BoujeeEnjinia1701/drumpanel/cad/drawings/DMP-DWG-001.pdf

CONCEPT, NOT FOR FABRICATION | DrumPanel · github.com/BoujeeEnjinia1701/drumpanel

FRONT VIEW
Scale 1:50; looking at the front (along +Y)

TOP VIEW
Scale 1:50; looking down (along -Z)

RIGHT VIEW
Scale 1:50; looking at the right side (along -X)

2182

4665 1340

ISOMETRIC VIEW
Not to scale; drums and panels not shown; seen from the front right and above, about 30 deg elevation

KEY DIMENSIONS (MM) AND DATA
Layout 2182 x 4665 x 1340 high (three stations in a row)
Drain stand at y -1500; saddles 500 apart; 2.9 deg fall to the bung end Cradle: rollers 380 apart at 310 high, under the hoops at +/-147
Drum axis 603; drum top 890; contact 33 deg from vertical
Rail posts at +/-712.5; rail beam top 1300; tool shelf on left post Shear discs 101 x 10, overlap 1.0; crank 155, 2.33:1
Ring head bolted on for ring cuts, nips 233 or 234 apart
Notches by lever punch: ends 60 x 35, hoops 40 x 32
End cutter wheel 50; cut line 552 dia; crank 150
Slip roll at y +1950: rolls 60 dia x 900 face
Sheet line 900; bending roll 90 behind, set 13.4 up (trial) Bending screws M20 x 1.5, dial 0.025 mm a division, lock nut Pinch gears m3 x 20 T; chain #40, 13 to 39 T; crank 300 Panels 233 / 234 / 233 x 1800; heads 552 dia
Masses (est.): cradle 196 kg, slip roll 191 kg, stand 15 kg PRELIMINARY, NOT FOR FABRICATION
REV | DESCRIPTION | DATE | BY
P1 | Preliminary GA from the constructable TRL 3 model (DMP-DDR-002) | 2026-10-03 | AC
P2 | Notching punch, ring head, raised head drive, dial adjusters, tool shelf (DMP-DDR-003) | 2026-10-03 | AC
DRUMPANEL | github.com/BoujeeEnjinia1701/drumpanel

## Drum opening bench set: general arrangement of the three stations

DRAWING NO.
DMP-DWG-001

REV
P2

SHEET
1 of 1

SIZE

## ANSI B

SCALE
1:50

UNITS
mm
PROJECTION | DATE
2026-10-03

DRAWN
Amish Chadha

MATERIAL / NOTES
S275 RHS and plate; C45 rolls; D2 discs; bronze bushes. See bom/bom.csv
Licensed CERN-OHL-S-2.0 · Design Molecule Lab · designmolecule.com | Generated from cad/src; do not edit by hand
