BoujeeEnjinia1701/drumpanel/cad/drawings/DMP-DWG-105.pdf

### BUILD PLAN SKETCH, PLAN NOT YET BUILT DrumPanel · github.com/BoujeeEnjinia1701/drumpanel

FRONT VIEW
Scale 1:10; looking at the front (along +Y)

TOP VIEW
Scale 1:10; looking down (along -Z)

RIGHT VIEW
Scale 1:10; looking at the right side (along -X)

120

200 946

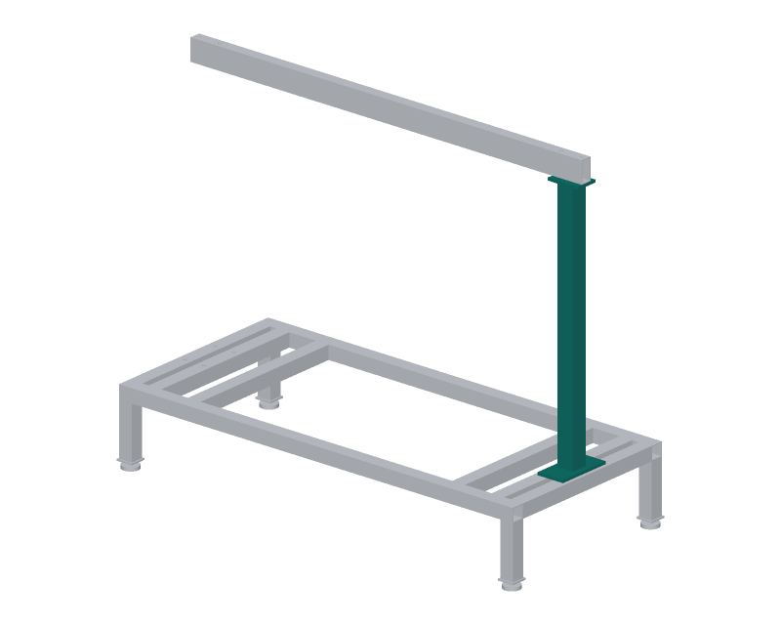
[picture p60: figure]

WHERE IT GOES
This part in colour, its neighbours in grey

HOW TO MAKE IT AND HOW IT FITS
Make two. Post: 60 x 60 x 4 mm RHS, 926.5 mm long, square ends. Base plate 200 x 100 x 10 mm: four 11 mm holes on a 75 x 140 mm rectangle (75 mm along the frame, 140 mm across it).
Cap plate 120 x 80 x 10 mm: two 11 mm holes on the centre line, 80 mm apart (40 mm each side of the post).
Weld the post to the middle of both plates, square both ways; check with a square before the welds cool.
Left post only: two 11 mm holes across it, 550 and 700 mm up from the frame top, for the tool shelf's two M10 through-bolts.
Fit: the base bolts across the two end cross members of the frame with 4 x M10 x 80; the rail beam sits on the cap and is held by
two M10 through-bolts. Post centre 712.5 mm from the middle. Check: post upright within 1 mm over its height when bolted.
REV | DESCRIPTION | DATE | BY
P1 | Making sketch for the prototype build plan | 2026-10-03 | AC
P2 | Amish's requirement decisions of 2026-10-03 (DMP-DDR-003) | 2026-10-03 | AC
DRUMPANEL | github.com/BoujeeEnjinia1701/drumpanel

## DrumPanel rail post (make 2): making sketch

DRAWING NO.
DMP-DWG-105

REV
P2

SHEET
1 of 1

SIZE

## ANSI B

SCALE
1:10

UNITS
mm
PROJECTION | DATE
2026-10-03

DRAWN
Amish Chadha

MATERIAL / NOTES
60 x 60 x 4 mm RHS; 10 mm plate; S275
Licensed CERN-OHL-S-2.0 · Design Molecule Lab · designmolecule.com | Generated from cad/src; do not edit by hand
