BoujeeEnjinia1701/drumpanel/cad/drawings/DMP-DWG-109.pdf

### BUILD PLAN SKETCH, PLAN NOT YET BUILT DrumPanel · github.com/BoujeeEnjinia1701/drumpanel

FRONT VIEW
Scale 1:5; looking at the front (along +Y)

TOP VIEW
Scale 1:5; looking down (along -Z)

RIGHT VIEW
Scale 1:5; looking at the right side (along -X)

195

148 272

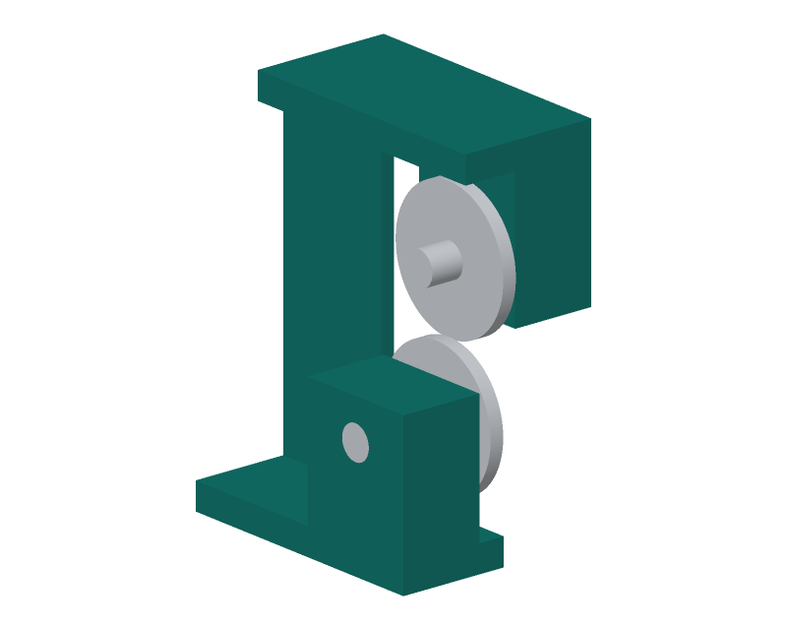
[picture p61: figure]

WHERE IT GOES
This part in colour, its neighbours in grey

HOW TO MAKE IT AND HOW IT FITS
Web: 10 mm plate 92 x 232 mm. It runs in the cut, behind the discs. Top plate 195 x 99 x 20 mm and lower plate 195 x 79 x 20 mm, welded across the top and bottom ends of the web.
Upper housing 90 x 60 x 101 mm on the top plate, beside the web; bore 57 mm on a line 49.5 mm above the nip for the eccentric bush (57 mm outside, 47 mm bore offset 3 mm) and one 6005 bearing. Lower housing 90 x 60 x 96 mm under the lower plate; bore 47 mm on a line 49.5 mm below the nip for two 6005 bearings.
Bore both housings in one setting so the shafts are parallel
within 0.05 mm over 60 mm; the disc faces must meet on one plane. Fit: the drop bar is welded to the top plate over the nip line;
four M8 tapped holes in the upper housing's outer face and the
top plate's end take the drive case. Make two frames: the second is the ring head (DMP-DWG-122).
Check: turning the eccentric moves the upper shaft 6 mm.
REV | DESCRIPTION | DATE | BY
P1 | Making sketch for the prototype build plan | 2026-10-03 | AC
P2 | Amish's requirement decisions of 2026-10-03 (DMP-DDR-003) | 2026-10-03 | AC
DRUMPANEL | github.com/BoujeeEnjinia1701/drumpanel

## DrumPanel rotary shear head frame: making sketch

DRAWING NO.
DMP-DWG-109

REV
P2

SHEET
1 of 1

SIZE

## ANSI B

SCALE
1:5

UNITS
mm
PROJECTION | DATE
2026-10-03

DRAWN
Amish Chadha

MATERIAL / NOTES
10 mm and 20 mm plate, S275; 6005-2RS bearings; eccentric bush
Licensed CERN-OHL-S-2.0 · Design Molecule Lab · designmolecule.com | Generated from cad/src; do not edit by hand
