BoujeeEnjinia1701/drumpanel/cad/drawings/DMP-DWG-110.pdf

### BUILD PLAN SKETCH, PLAN NOT YET BUILT DrumPanel · github.com/BoujeeEnjinia1701/drumpanel

FRONT VIEW
Scale 1:5; looking at the front (along +Y)

TOP VIEW
Scale 1:5; looking down (along -Z)

RIGHT VIEW
Scale 1:5; looking at the right side (along -X)

25

170 125

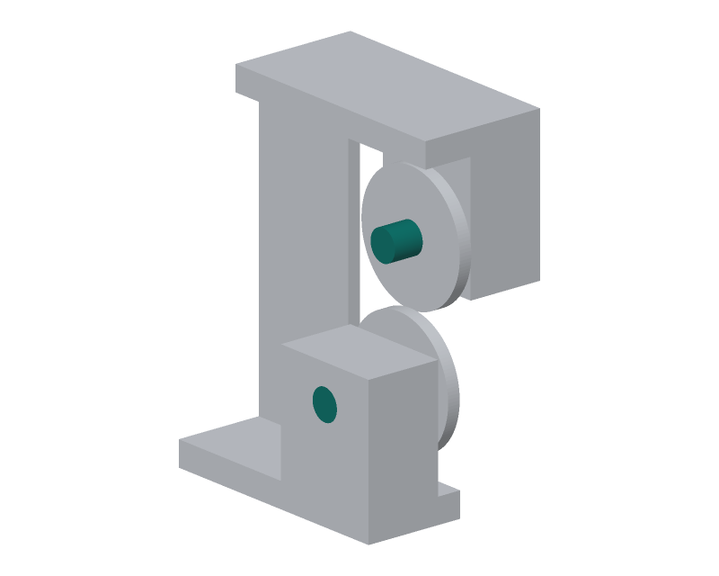
[picture p62: figure]

WHERE IT GOES
This part in colour, its neighbours in grey

HOW TO MAKE IT AND HOW IT FITS
Upper shaft: 25 mm, 120 mm long: a 24 mm stub on the disc side for the ring head coupling (a 6 mm cross slot in its end), a 35 mm shoulder at the disc, and a keyway at the far end for the 15 tooth sprocket inside the drive case.
Lower shaft: 25 mm, 74 mm long, with the same shoulder.
Discs (bought): 101 x 10 mm D2, hardened 58 to 60 HRC, 25 mm bore. Each is clamped against its shoulder by a countersunk M8 end screw and washer that sit below the cutting face (upper disc: a clamp collar on the stub instead).
Fit: cutting faces meet on the cut plane with no gap and no rub; shim behind a disc with 0.05 mm shims to get there.
Set the overlap to 1.0 mm with the eccentric and lock it.
Make a second set for the ring head (DMP-DWG-122).
REV | DESCRIPTION | DATE | BY
P1 | Making sketch for the prototype build plan | 2026-10-03 | AC
P2 | Amish's requirement decisions of 2026-10-03 (DMP-DDR-003) | 2026-10-03 | AC
DRUMPANEL | github.com/BoujeeEnjinia1701/drumpanel

## DrumPanel head shafts and discs: making sketch

DRAWING NO.
DMP-DWG-110

REV
P2

SHEET
1 of 1

SIZE

## ANSI B

SCALE
1:5

UNITS
mm
PROJECTION | DATE
2026-10-03

DRAWN
Amish Chadha

MATERIAL / NOTES
25 mm bright bar; bought D2 discs
Licensed CERN-OHL-S-2.0 · Design Molecule Lab · designmolecule.com | Generated from cad/src; do not edit by hand
