BoujeeEnjinia1701/drumpanel/cad/drawings/DMP-DWG-116.pdf

### BUILD PLAN SKETCH, PLAN NOT YET BUILT DrumPanel · github.com/BoujeeEnjinia1701/drumpanel

FRONT VIEW
Scale 1:10; looking at the front (along +Y)

TOP VIEW
Scale 1:10; looking down (along -Z)

RIGHT VIEW
Scale 1:10; looking at the right side (along -X)

1050

190 268

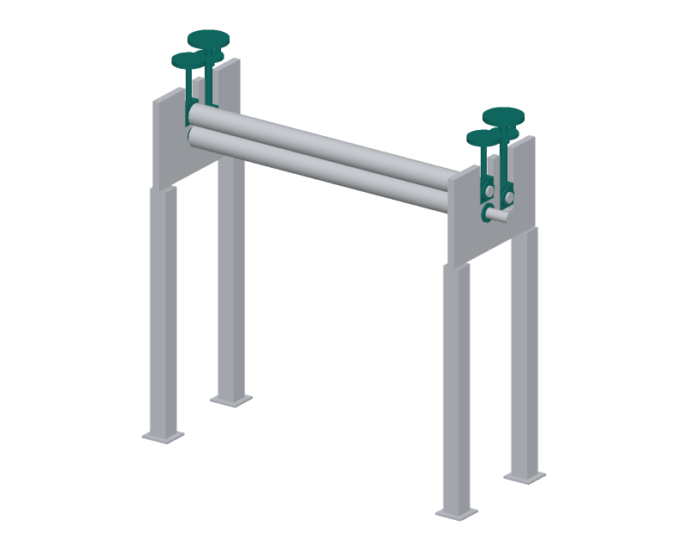
[picture p63: figure]

WHERE IT GOES
This part in colour, its neighbours in grey

HOW TO MAKE IT AND HOW IT FITS
Four slide blocks, 60 x 60 x 20 mm (20 mm thick = the side plate), bored 40 mm in the middle for a flanged bronze bush.
Fit in the 60 mm slots with 0.2 mm clearance; break the edges. Six flanged bronze bushes 30 x 40 x 20 mm, 52 mm flange 6 mm thick, pressed in from the outside; a grease hole in each.
A 3 mm keeper plate on the inside face holds each block in.
Pinch screws M16 x 120 (two) with 90 mm handwheels. Bending screws M20 x 1.5 fine pitch, 150 mm (two), with 110 mm handwheels. Each screw has a collar captured in the top of its block.
Bending roll adjuster on each bending screw: an M20 x 1.5 lock nut on the bridge; an 80 mm dial of 60 divisions (0.025 mm each), clamped to the screw by a set screw; a pointer screwed to the bridge, its tip over the dial rim.
Fit: the screws run in the threaded holes of the top bridges. Check: each block slides its full travel; one turn of a bending screw moves its roll 1.5 mm; the lock nut holds the setting.
REV | DESCRIPTION | DATE | BY
P1 | Making sketch for the prototype build plan | 2026-10-03 | AC
P2 | Amish's requirement decisions of 2026-10-03 (DMP-DDR-003) | 2026-10-03 | AC
DRUMPANEL | github.com/BoujeeEnjinia1701/drumpanel

## DrumPanel slide blocks, bushes, screws and dials: making sketch

DRAWING NO.
DMP-DWG-116

REV
P2

SHEET
1 of 1

SIZE

## ANSI B

SCALE
1:10

UNITS
mm
PROJECTION | DATE
2026-10-03

DRAWN
Amish Chadha

MATERIAL / NOTES
20 mm steel plate; bronze bushes; M16 and M20 x 1.5 screws; dials
Licensed CERN-OHL-S-2.0 · Design Molecule Lab · designmolecule.com | Generated from cad/src; do not edit by hand
