BoujeeEnjinia1701/drumpanel/cad/drawings/DMP-DWG-120.pdf

### BUILD PLAN SKETCH, PLAN NOT YET BUILT DrumPanel · github.com/BoujeeEnjinia1701/drumpanel

FRONT VIEW
Scale 1:5; looking at the front (along +Y)

TOP VIEW
Scale 1:5; looking down (along -Z)

RIGHT VIEW
Scale 1:5; looking at the right side (along -X)

140

156 309

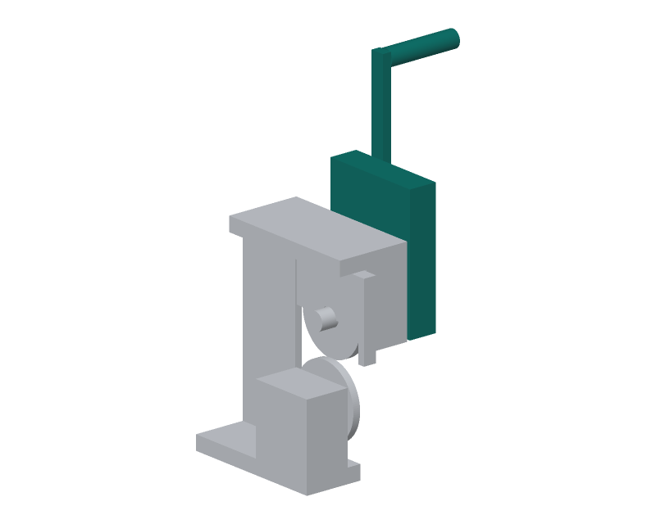
[picture p64: figure]

WHERE IT GOES
This part in colour, its neighbours in grey

HOW TO MAKE IT AND HOW IT FITS
Two plates 140 x 182 x 8 mm, 22 mm apart, joined by a 1.5 mm sheet band all round: the band is the chain guard.
Bores (both plates, drilled together): upper shaft 26 mm clear on the disc line; jackshaft 42 mm for a 6004 bearing, 80 mm above it; crank shaft 42 mm for a 6004 bearing, 60 mm back and 120 mm above the disc line.
Sprockets #35: 15 teeth on the upper shaft and on the jackshaft (first chain, 1 to 1); 28 teeth on the jackshaft and 12 teeth on
the crank shaft (second chain, 2.33 to 1).
Crank: 20 x 12 mm arm, 155 mm between centres, 24 mm grip 100 mm long free to spin; it turns well clear of the drum.
Fit: inner plate bolted to the upper housing and the top plate
with four M8 screws.
Check: 2.33 crank turns turn the discs once; nothing rubs.
REV | DESCRIPTION | DATE | BY
P1 | Making sketch for the prototype build plan | 2026-10-03 | AC
DRUMPANEL | github.com/BoujeeEnjinia1701/drumpanel

## DrumPanel shear head drive case and crank: making sketch

DRAWING NO.
DMP-DWG-120

REV
P1

SHEET
1 of 1

SIZE

## ANSI B

SCALE
1:5

UNITS
mm
PROJECTION | DATE
2026-10-03

DRAWN
Amish Chadha

MATERIAL / NOTES
8 mm plate; 1.5 mm sheet; 20 mm bar; #35 sprockets and chain; 6004-2RS bearings
Licensed CERN-OHL-S-2.0 · Design Molecule Lab · designmolecule.com | Generated from cad/src; do not edit by hand
