BoujeeEnjinia1701/drumpanel/cad/drawings/DMP-DWG-121.pdf

### BUILD PLAN SKETCH, PLAN NOT YET BUILT DrumPanel · github.com/BoujeeEnjinia1701/drumpanel

FRONT VIEW
Scale 1:5; looking at the front (along +Y)

TOP VIEW
Scale 1:5; looking down (along -Z)

RIGHT VIEW
Scale 1:5; looking at the right side (along -X)

435

76 200

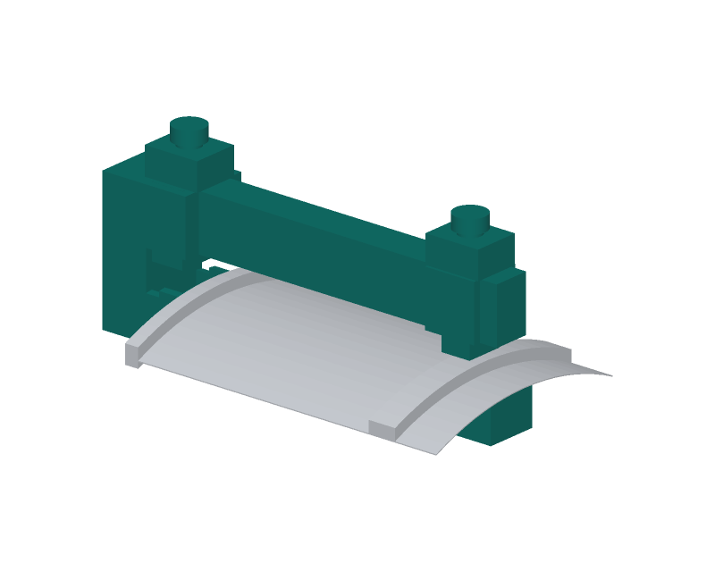
[picture p65: figure]

WHERE IT GOES
This part in colour, its neighbours in grey

HOW TO MAKE IT AND HOW IT FITS
C-frame from S355 plate: back 50 x 76 x 150 mm; lower jaw 56 x 50 mm and upper jaw 40 x 60 mm, 385 mm long; gap 40 mm. Die faces ground to the drum's inside radius (286 mm; 280 mm at the chime station).
Station 1, at the back: open-ended chime notch 60 x 35 mm. Station 2, 338 mm out: hoop slot 40 x 32 mm.
Punches D2, faces raked 10 degrees (roof shape); dies D2, punch to die clearance 0.1 to 0.2 mm a side; harden both.
Each punch is pushed by a Tr24 x 5 screw in a bronze nut block, through a needle thrust bearing; 500 mm ratchet lever.
Fit: chime: back face on the drum end. Hoop: drum end against the station 1 die block, jaw in through the chime notch.
Check: a punch enters its die by hand with even clearance.
REV | DESCRIPTION | DATE | BY
P1 | Making sketch for the prototype build plan | 2026-10-03 | AC
DRUMPANEL | github.com/BoujeeEnjinia1701/drumpanel

## DrumPanel lever notching punch: making sketch

DRAWING NO.
DMP-DWG-121

REV
P1

SHEET
1 of 1

SIZE

## ANSI B

SCALE
1:5

UNITS
mm
PROJECTION | DATE
2026-10-03

DRAWN
Amish Chadha

MATERIAL / NOTES
S355 plate; D2 punches and dies; Tr24 x 5 screws in bronze nuts
Licensed CERN-OHL-S-2.0 · Design Molecule Lab · designmolecule.com | Generated from cad/src; do not edit by hand
