BoujeeEnjinia1701/drumpanel/cad/drawings/DMP-DWG-122.pdf

### BUILD PLAN SKETCH, PLAN NOT YET BUILT DrumPanel · github.com/BoujeeEnjinia1701/drumpanel

FRONT VIEW
Scale 1:5; looking at the front (along +Y)

TOP VIEW
Scale 1:5; looking down (along -Z)

RIGHT VIEW
Scale 1:5; looking at the right side (along -X)

160

270 112

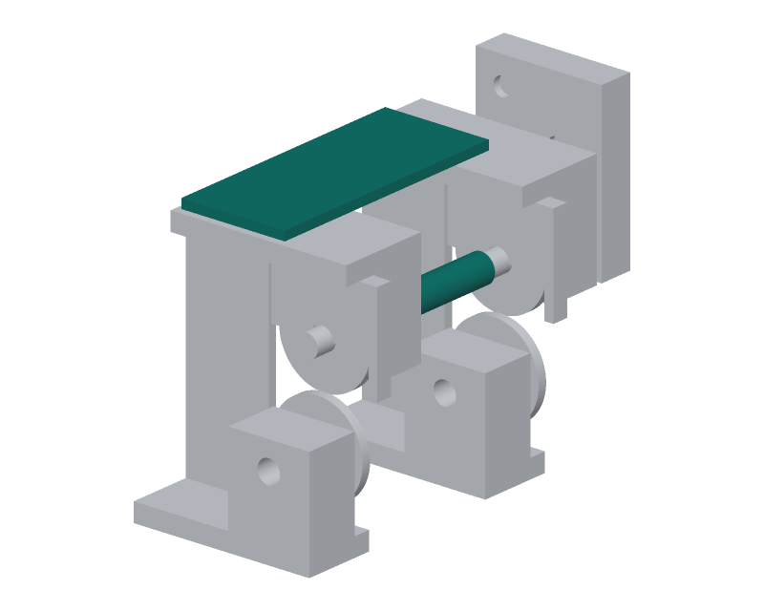
[picture p66: figure]

WHERE IT GOES
This part in colour, its neighbours in grey

HOW TO MAKE IT AND HOW IT FITS
The ring head is a second shear head made to DMP-DWG-109 to 111 with no drive; this sheet adds the parts that join it on.
Spacer plate 115 x 270 x 10 mm: four 13 mm holes over each top plate; the ring head end slotted so the nips sit 233 or 234 mm
apart (the middle pass is 234 mm).
Coupling shaft: 25 mm bar 135 mm long, a 6 mm dog across each end to engage the cross slots in the two upper shaft stubs.
Guard sleeve: loose plastic tube 31 mm outside over the coupling. Fit: with the main head swivelled for ring cuts, lower the ring
head through the slit, engage the coupling, bolt the plate.
Check: both upper discs turn together with the crank.
REV | DESCRIPTION | DATE | BY
P1 | Making sketch for the prototype build plan | 2026-10-03 | AC
DRUMPANEL | github.com/BoujeeEnjinia1701/drumpanel

## DrumPanel ring head spacer plate and coupling: making sketch

DRAWING NO.
DMP-DWG-122

REV
P1

SHEET
1 of 1

SIZE

## ANSI B

SCALE
1:5

UNITS
mm
PROJECTION | DATE
2026-10-03

DRAWN
Amish Chadha

MATERIAL / NOTES
10 mm plate; 25 mm bright bar; plastic tube
Licensed CERN-OHL-S-2.0 · Design Molecule Lab · designmolecule.com | Generated from cad/src; do not edit by hand
