BoujeeEnjinia1701/drumpanel/cad/drawings/DMP-DWG-123.pdf

### BUILD PLAN SKETCH, PLAN NOT YET BUILT DrumPanel · github.com/BoujeeEnjinia1701/drumpanel

FRONT VIEW
Scale 1:10; looking at the front (along +Y)

TOP VIEW
Scale 1:10; looking down (along -Z)

RIGHT VIEW
Scale 1:10; looking at the right side (along -X)

380

600 310

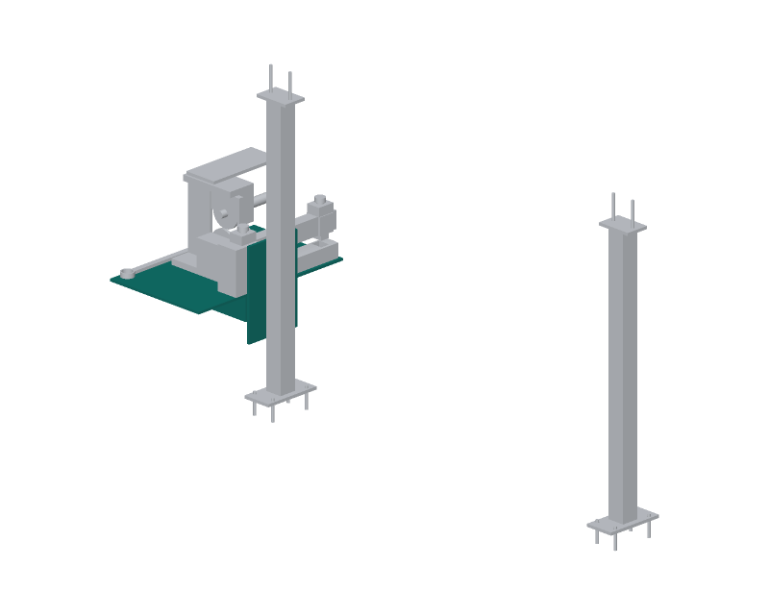
[picture p67: figure]

WHERE IT GOES
This part in colour, its neighbours in grey

HOW TO MAKE IT AND HOW IT FITS
Back plate 200 x 310 x 10 mm with two 11 mm holes on its centre line, 150 mm apart, matching the holes in the left post.
Shelf 380 x 600 x 6 mm, welded square to the back plate 150 mm above its bottom edge.
Two brackets 250 x 80 x 6 mm under the shelf, 200 mm apart, welded to the shelf and the back plate.
Fit: bolted to the outer face of the left post with two M10 through-bolts; the shelf top 608 mm from the floor.
It holds the notching punch, its lever and the ring head with its spacer plate and coupling (about 40 kg).
Check: level both ways; no movement when loaded by hand.
REV | DESCRIPTION | DATE | BY
P1 | Making sketch for the prototype build plan | 2026-10-03 | AC
DRUMPANEL | github.com/BoujeeEnjinia1701/drumpanel

## DrumPanel tool shelf on the left rail post: making sketch

DRAWING NO.
DMP-DWG-123

REV
P1

SHEET
1 of 1

SIZE

## ANSI B

SCALE
1:10

UNITS
mm
PROJECTION | DATE
2026-10-03

DRAWN
Amish Chadha

MATERIAL / NOTES
6 mm and 10 mm plate, S275; M10 bolts
Licensed CERN-OHL-S-2.0 · Design Molecule Lab · designmolecule.com | Generated from cad/src; do not edit by hand
