BoujeeEnjinia1701/drumpanel/cad/drawings/DMP-DWG-101.pdf

### BUILD PLAN SKETCH, PLAN NOT YET BUILT DrumPanel · github.com/BoujeeEnjinia1701/drumpanel

FRONT VIEW
Scale 1:10; looking at the front (along +Y)

TOP VIEW
Scale 1:10; looking down (along -Z)

RIGHT VIEW
Scale 1:10; looking at the right side (along -X)

800

560 410

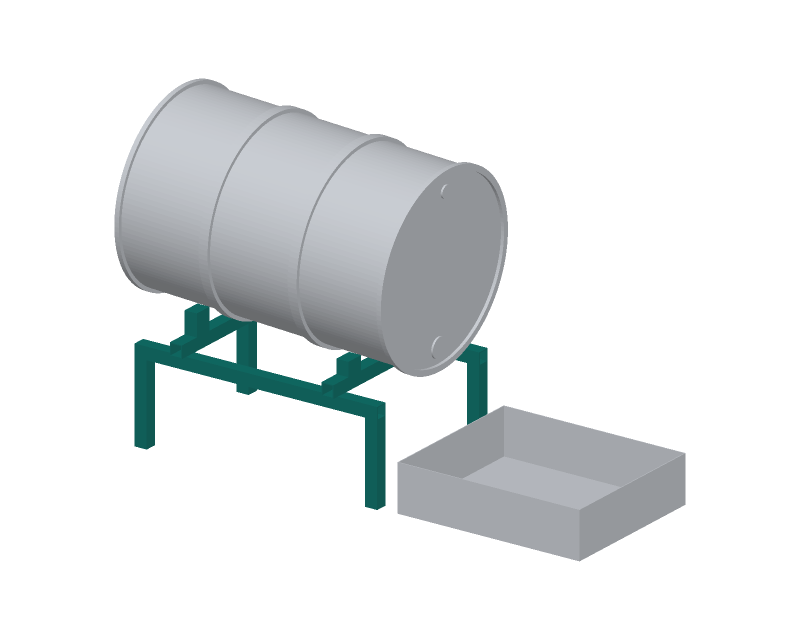
[picture p68: figure]

WHERE IT GOES
This part in colour, its neighbours in grey

HOW TO MAKE IT AND HOW IT FITS
Two rails 800 mm long, 480 mm apart (centres), on four legs 260 mm tall at the rail ends. Weld legs under the rails, square.
Two saddles 560 mm long across the rails, 500 mm apart (centres), welded on top of the rails. Top of the saddles 340 mm from the floor. Chocks: four hardwood blocks 40 x 60 mm, inner faces 300 mm apart. 70 mm tall on the far saddle, 45 mm tall on the bung-end saddle,
so the drum falls 2.9 degrees toward its bungs. Screw them down. Fit: the drum body rests on the four inner top edges of the chocks, bung end low and over the tray. Nothing else holds it.
Loads: a drum full of water is about 240 kg; 691 N on each chock. Check: frame stands level without rocking; the drum, rolled on, sits on all four chocks and does not roll off sideways.
REV | DESCRIPTION | DATE | BY
P1 | Making sketch for the prototype build plan | 2026-10-03 | AC
DRUMPANEL | github.com/BoujeeEnjinia1701/drumpanel

## DrumPanel drain and purge stand: making sketch

DRAWING NO.
DMP-DWG-101

REV
P1

SHEET
1 of 1

SIZE

## ANSI B

SCALE
1:10

UNITS
mm
PROJECTION | DATE
2026-10-03

DRAWN
Amish Chadha

MATERIAL / NOTES
40 x 40 x 3 mm RHS, S275; hardwood chocks 40 x 60 mm
Licensed CERN-OHL-S-2.0 · Design Molecule Lab · designmolecule.com | Generated from cad/src; do not edit by hand
