BoujeeEnjinia1701/drumpanel/cad/drawings/DMP-DWG-102.pdf

### BUILD PLAN SKETCH, PLAN NOT YET BUILT DrumPanel · github.com/BoujeeEnjinia1701/drumpanel

FRONT VIEW
Scale 1:20; looking at the front (along +Y)

TOP VIEW
Scale 1:20; looking down (along -Z)

RIGHT VIEW
Scale 1:20; looking at the right side (along -X)

1560

710 248

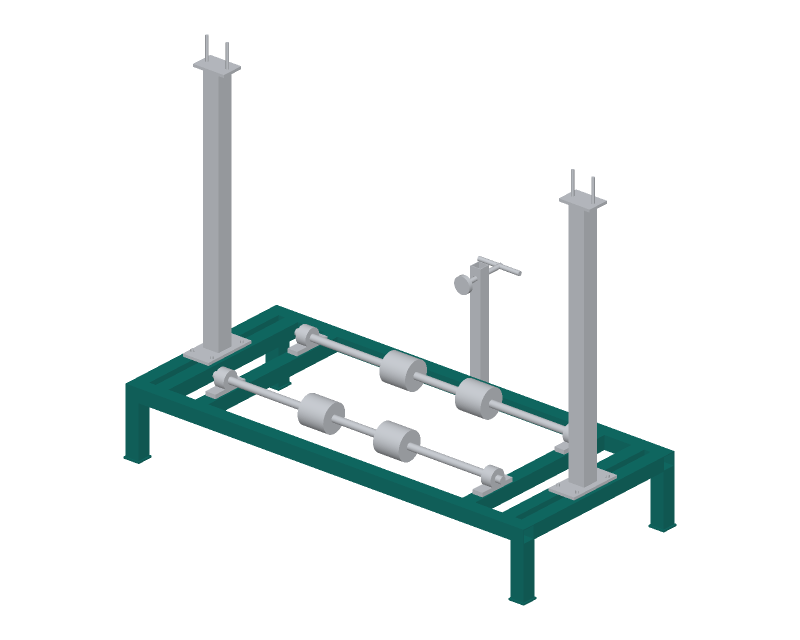
[picture p69: figure]

WHERE IT GOES
This part in colour, its neighbours in grey

HOW TO MAKE IT AND HOW IT FITS
Two side rails 1,550 mm long, outer faces 700 mm apart.
Six cross members 600 mm long between the rails, centred 520, 675 and 750 mm each side of the middle (the last one flush with the ends). Four legs 192 mm long under the corners, each with a 60 x 60 x 6 mm foot plate and an M12 nut welded on it for a levelling foot.
Top of the frame 273.5 mm from the floor with the feet screwed in
13 mm. Weld on a flat table; check the diagonals agree within 2 mm. Holes, 11 mm: two for each pillow block on the 520 mm members, 137.5 and 242.5 mm each side of the centre line; four for each post base, 70 mm each side of the centre line on the 675 and 750 members. Fit: pillow blocks and post bases bolt on top with M10; the brake
post bolts to the outer face of a side rail at the middle.
Check: frame top flat within 2 mm when the feet are set.
REV | DESCRIPTION | DATE | BY
P1 | Making sketch for the prototype build plan | 2026-10-03 | AC
DRUMPANEL | github.com/BoujeeEnjinia1701/drumpanel

## DrumPanel cradle frame: making sketch

DRAWING NO.
DMP-DWG-102

REV
P1

SHEET
1 of 1

SIZE

## ANSI B

SCALE
1:20

UNITS
mm
PROJECTION | DATE
2026-10-03

DRAWN
Amish Chadha

MATERIAL / NOTES
50 x 50 x 3 mm RHS, S275; 6 mm foot plates; M12 nuts
Licensed CERN-OHL-S-2.0 · Design Molecule Lab · designmolecule.com | Generated from cad/src; do not edit by hand
