BoujeeEnjinia1701/drumpanel/cad/drawings/DMP-DWG-103.pdf

### BUILD PLAN SKETCH, PLAN NOT YET BUILT DrumPanel · github.com/BoujeeEnjinia1701/drumpanel

FRONT VIEW
Scale 1:10; looking at the front (along +Y)

TOP VIEW
Scale 1:10; looking down (along -Z)

RIGHT VIEW
Scale 1:10; looking at the right side (along -X)

1120

102 102

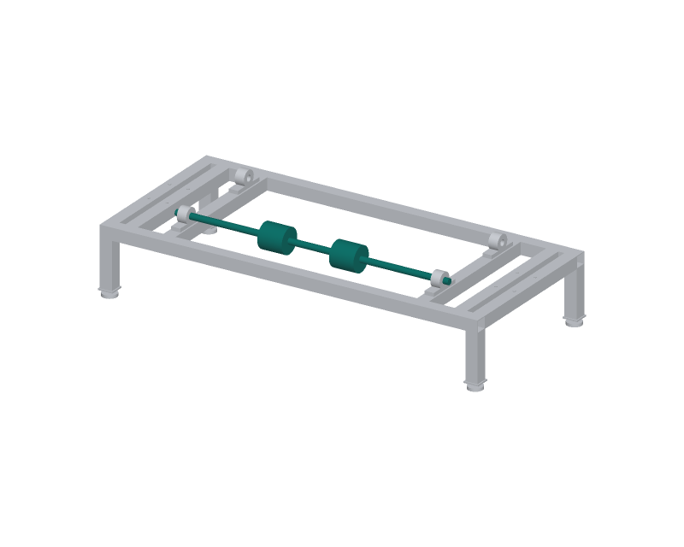
[picture p70: figure]

WHERE IT GOES
This part in colour, its neighbours in grey

HOW TO MAKE IT AND HOW IT FITS
Make two. Shaft: 25 mm bright bar, 1,120 mm long, ends chamfered. Rollers: 101.6 x 4 mm tube cut 100 mm long; two 10 mm discs
93 mm across, bored 25 mm, welded into each end of the tube. Slide two rollers on, centred 147 mm each side of the middle of the shaft (294 mm apart, under the drum's rolling hoops).
Weld each disc to the shaft all round; skim the roller faces true
in a lathe if they run out more than 0.5 mm.
Fit: the shaft runs in two UCP205 pillow blocks, 1,040 mm apart, grub screws tightened on the shaft. Shaft centres 380 mm apart. Check: the shaft turns freely by hand in its blocks; the rollers run true within 0.5 mm.
REV | DESCRIPTION | DATE | BY
P1 | Making sketch for the prototype build plan | 2026-10-03 | AC
DRUMPANEL | github.com/BoujeeEnjinia1701/drumpanel

## DrumPanel roller shaft with two rollers (make 2): making sketch

DRAWING NO.
DMP-DWG-103

REV
P1

SHEET
1 of 1

SIZE

## ANSI B

SCALE
1:10

UNITS
mm
PROJECTION | DATE
2026-10-03

DRAWN
Amish Chadha

MATERIAL / NOTES
25 mm bright steel bar; 101.6 x 4 mm tube; 10 mm plate discs
Licensed CERN-OHL-S-2.0 · Design Molecule Lab · designmolecule.com | Generated from cad/src; do not edit by hand
