BoujeeEnjinia1701/drumpanel/cad/drawings/DMP-DWG-104.pdf

### BUILD PLAN SKETCH, PLAN NOT YET BUILT DrumPanel · github.com/BoujeeEnjinia1701/drumpanel

FRONT VIEW
Scale 1:5; looking at the front (along +Y)

TOP VIEW
Scale 1:5; looking down (along -Z)

RIGHT VIEW
Scale 1:5; looking at the right side (along -X)

160

183 460

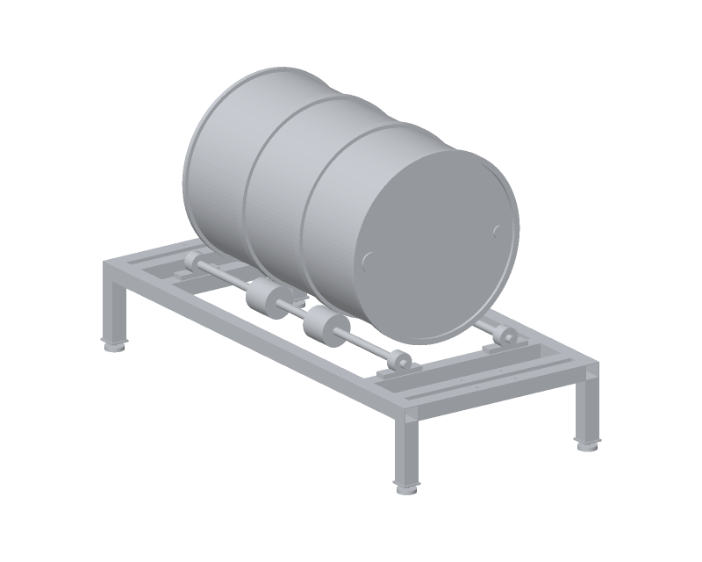
[picture p71: figure]

WHERE IT GOES
This part in colour, its neighbours in grey

HOW TO MAKE IT AND HOW IT FITS
Post: 40 x 40 x 3 mm RHS, 460 mm long. Two 11 mm holes through it, 25 mm apart, 56 and 81 mm up from its foot, to bolt it to the rail.
An 18 mm hole through both walls 423 mm up from its foot; weld an M16 nut over the hole on the outer face (away from the drum). Screw: M16 x 200; weld a 16 mm bar 160 mm long across its head as a T-handle. A 60 mm rubber pad 15 mm thick on a swivel plate at its tip faces the drum.
Fit: post bolted with 2 x M10 to the outer face of the right side
rail at the middle of the frame. Screwed in, the pad presses on the drum side between the hoops at the height of the drum axis. Check: with the screw tight the drum cannot be turned by hand.
REV | DESCRIPTION | DATE | BY
P1 | Making sketch for the prototype build plan | 2026-10-03 | AC
DRUMPANEL | github.com/BoujeeEnjinia1701/drumpanel

## DrumPanel drum brake: making sketch

DRAWING NO.
DMP-DWG-104

REV
P1

SHEET
1 of 1

SIZE

## ANSI B

SCALE
1:5

UNITS
mm
PROJECTION | DATE
2026-10-03

DRAWN
Amish Chadha

MATERIAL / NOTES
40 x 40 x 3 mm RHS; M16 x 200 screw; 16 mm bar; rubber pad
Licensed CERN-OHL-S-2.0 · Design Molecule Lab · designmolecule.com | Generated from cad/src; do not edit by hand
