BoujeeEnjinia1701/drumpanel/cad/drawings/DMP-DWG-106.pdf

### BUILD PLAN SKETCH, PLAN NOT YET BUILT DrumPanel · github.com/BoujeeEnjinia1701/drumpanel

FRONT VIEW
Scale 1:10; looking at the front (along +Y)

TOP VIEW
Scale 1:10; looking down (along -Z)

RIGHT VIEW
Scale 1:10; looking at the right side (along -X)

1540

40 80

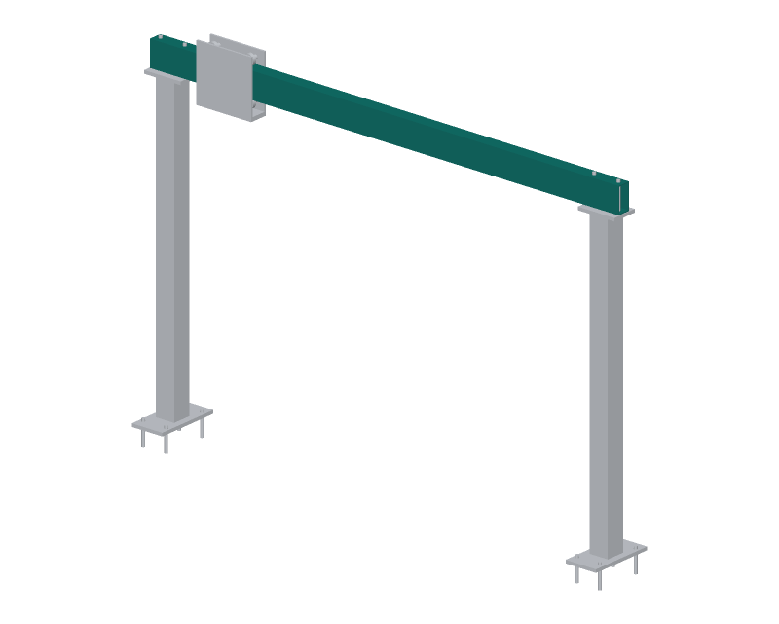
[picture p72: figure]

WHERE IT GOES
This part in colour, its neighbours in grey

HOW TO MAKE IT AND HOW IT FITS
Rail beam: 80 x 40 x 3 mm RHS, 1,540 mm long, stood on its narrow edge (80 mm tall). The top face is the trolley track: keep it
clean and free of weld spatter; file any seam bead flat.
Holes: two 11 mm vertical holes through both walls at each end, 17.5 and 97.5 mm from the end, on the centre line.
Crush tubes: 14 mm tube 74 mm long inside the beam at each hole so the through-bolts do not crush it.
Fit: each end sits on a post cap, held by two M10 x 110 bolts;
the bolt heads on top stop the trolley at the ends.
Check: the top face is straight within 1 mm over its length (a taut string or a straightedge).
REV | DESCRIPTION | DATE | BY
P1 | Making sketch for the prototype build plan | 2026-10-03 | AC
DRUMPANEL | github.com/BoujeeEnjinia1701/drumpanel

## DrumPanel rail beam: making sketch

DRAWING NO.
DMP-DWG-106

REV
P1

SHEET
1 of 1

SIZE

## ANSI B

SCALE
1:10

UNITS
mm
PROJECTION | DATE
2026-10-03

DRAWN
Amish Chadha

MATERIAL / NOTES
80 x 40 x 3 mm RHS, S275; 14 mm tube
Licensed CERN-OHL-S-2.0 · Design Molecule Lab · designmolecule.com | Generated from cad/src; do not edit by hand
