BoujeeEnjinia1701/drumpanel/cad/drawings/DMP-DWG-107.pdf

### BUILD PLAN SKETCH, PLAN NOT YET BUILT DrumPanel · github.com/BoujeeEnjinia1701/drumpanel

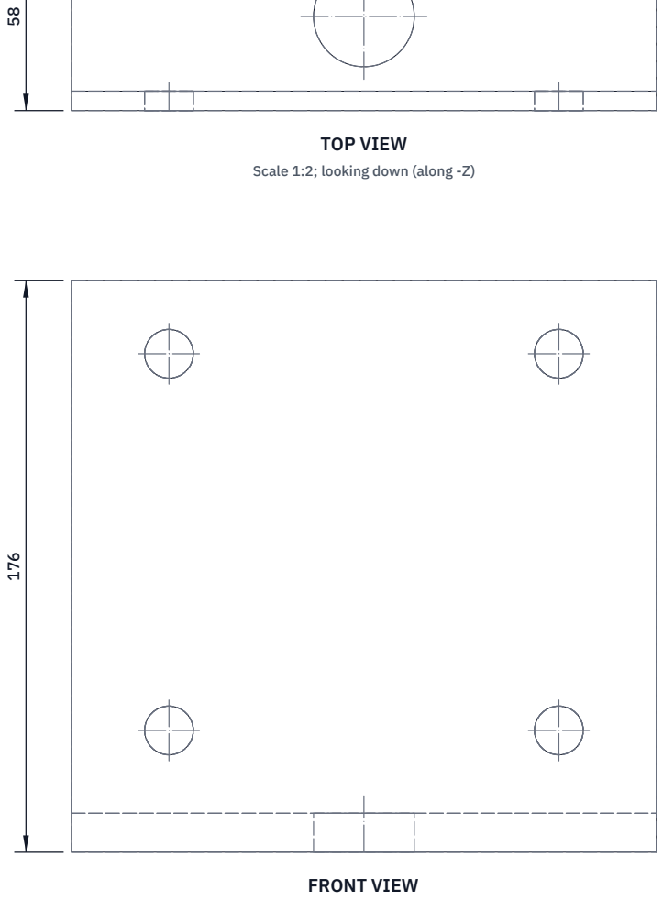
[picture p73: figure]
FRONT VIEW; TOP VIEW; Scale 1:2; looking down (along -Z)

Scale 1:2; looking at the front (along +Y)

RIGHT VIEW
Scale 1:2; looking at the right side (along -X)

180

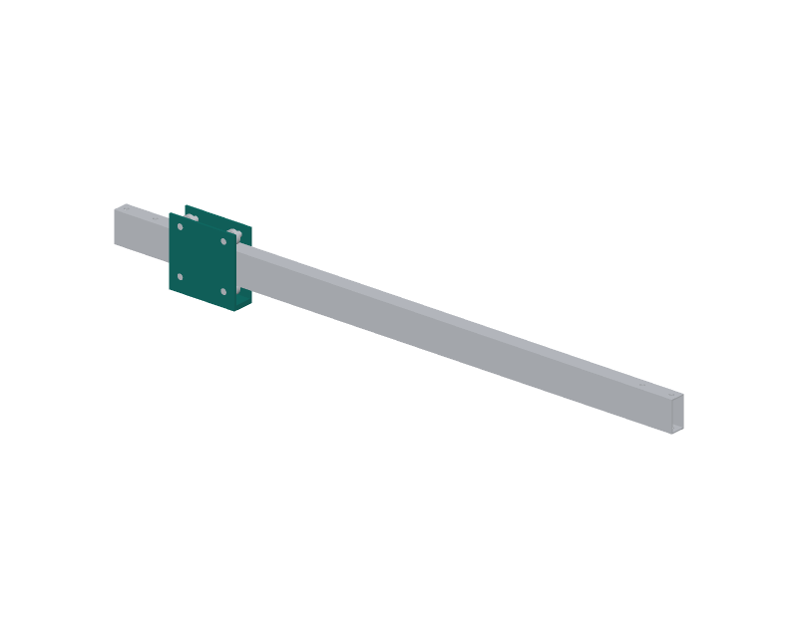
[picture p74: figure]

WHERE IT GOES
This part in colour, its neighbours in grey

HOW TO MAKE IT AND HOW IT FITS
Two side plates 180 x 164 x 6 mm. Four 15.5 mm axle holes in each, 60 mm each side of the middle, 141.5 and 25.5 mm up from the bottom edge. Drill the two plates clamped together.
Swivel plate 180 x 58 x 12 mm, welded under both side plates so their inner faces are 46 mm apart (beam 40 mm, 3 mm each side). Pivot hole 31 mm in the middle of the swivel plate; two 10.5 mm index holes 45 mm from it, at 0 and 90 degrees.
Wheels: 6202-2RS bearings on 15 mm axles with spacers; two ride on top of the beam and two run 1 mm under it (anti-lift).
Fit: slide on from the beam end before the end bolts go in, or
drop on from above and fit the lower axles after.
Check: rolls the full length by hand, no tight spots.
REV | DESCRIPTION | DATE | BY
P1 | Making sketch for the prototype build plan | 2026-10-03 | AC
DRUMPANEL | github.com/BoujeeEnjinia1701/drumpanel

## DrumPanel trolley with swivel plate: making sketch

DRAWING NO.
DMP-DWG-107

REV
P1

SHEET
1 of 1

SIZE

## ANSI B

SCALE
1:2

UNITS
mm
PROJECTION | DATE
2026-10-03

DRAWN
Amish Chadha

MATERIAL / NOTES
6 mm and 12 mm plate, S275; four 6202-2RS bearings; 15 mm bar
Licensed CERN-OHL-S-2.0 · Design Molecule Lab · designmolecule.com | Generated from cad/src; do not edit by hand
