BoujeeEnjinia1701/drumpanel/cad/drawings/DMP-DWG-108.pdf

### BUILD PLAN SKETCH, PLAN NOT YET BUILT DrumPanel · github.com/BoujeeEnjinia1701/drumpanel

FRONT VIEW
Scale 1:5; looking at the front (along +Y)

TOP VIEW
Scale 1:5; looking down (along -Z)

RIGHT VIEW
Scale 1:5; looking at the right side (along -X)

120

120 159

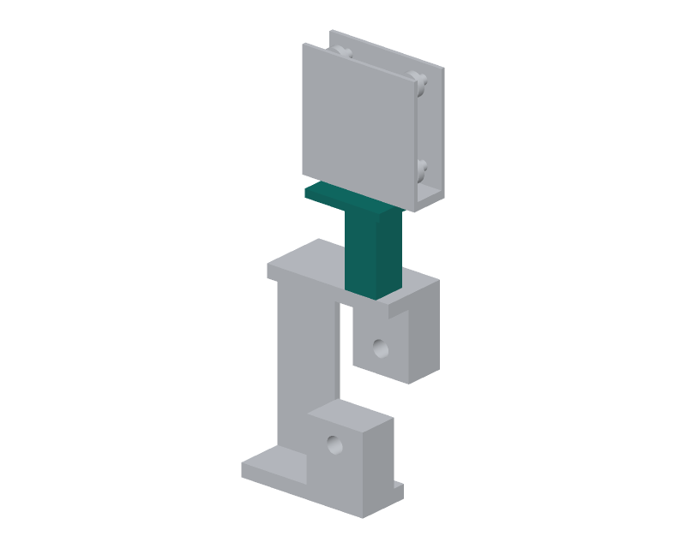
[picture p75: figure]

WHERE IT GOES
This part in colour, its neighbours in grey

HOW TO MAKE IT AND HOW IT FITS
Head plate 120 x 120 x 12 mm: a 31 mm hole in the middle for the pivot pin and a 10.5 mm hole 45 mm from it for the index pin. Drop bar: 50 x 50 x 4 mm RHS, 126 mm long, welded square under the head plate, centred, and at its lower end to the middle of
the shear head's top plate (over the nip line).
Pivot pin: 30 mm bar 55 mm long with a 40 mm collar welded at its top; a 6 mm hole for an R-clip under the swivel plate.
Index pin: 10 mm, on a lanyard, through the head plate into one of the two holes in the swivel plate: slit or ring position.
Fit: the head hangs from the trolley on the pivot pin and turns through 90 degrees when the index pin is out.
Check: the head swings freely; the index pin drops in at both positions.
REV | DESCRIPTION | DATE | BY
P1 | Making sketch for the prototype build plan | 2026-10-03 | AC
DRUMPANEL | github.com/BoujeeEnjinia1701/drumpanel

## DrumPanel drop bar, head plate and pivot pin: making sketch

DRAWING NO.
DMP-DWG-108

REV
P1

SHEET
1 of 1

SIZE

## ANSI B

SCALE
1:5

UNITS
mm
PROJECTION | DATE
2026-10-03

DRAWN
Amish Chadha

MATERIAL / NOTES
50 x 50 x 4 mm RHS; 12 mm plate; 30 mm bar
Licensed CERN-OHL-S-2.0 · Design Molecule Lab · designmolecule.com | Generated from cad/src; do not edit by hand
