BoujeeEnjinia1701/drumpanel/cad/drawings/DMP-DWG-111.pdf

### BUILD PLAN SKETCH, PLAN NOT YET BUILT DrumPanel · github.com/BoujeeEnjinia1701/drumpanel

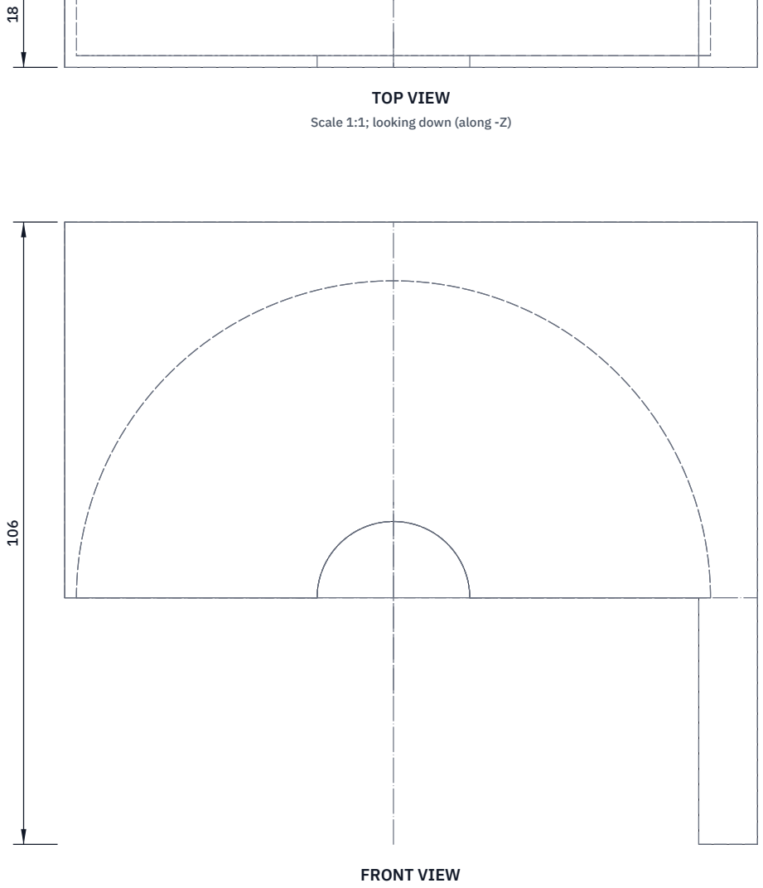
[picture p76: figure]
FRONT VIEW; TOP VIEW; Scale 1:1; looking down (along -Z)

Scale 1:1; looking at the front (along +Y)

RIGHT VIEW
Scale 1:1; looking at the right side (along -X)

118

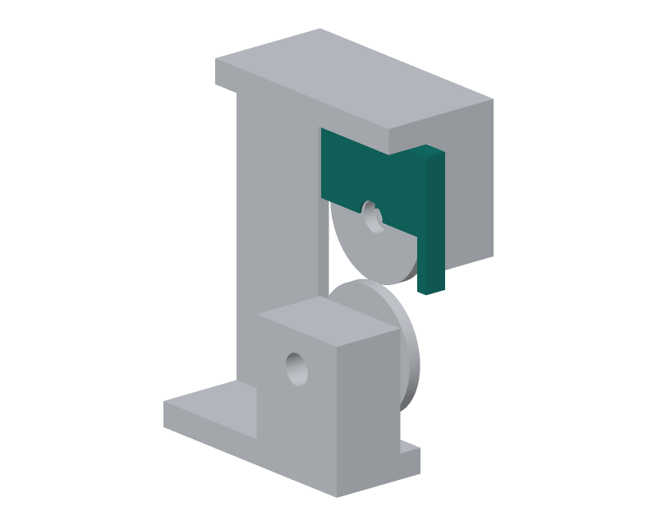
[picture p77: figure]

WHERE IT GOES
This part in colour, its neighbours in grey

HOW TO MAKE IT AND HOW IT FITS
A hood over the upper disc: 1.5 mm sheet, 118 mm long, 18 mm wide outside, 64 mm tall, with a 108 mm arched opening for the disc. Front skirt: a 10 mm deep plate down the front of the hood, ending 8 mm above the sheet line and 52 mm ahead of the nip, so a
finger cannot reach the nip from the front.
A 26 mm hole in the back face for the upper shaft.
Fit: two M5 screws into the upper housing; it does not touch the disc (at least 2 mm clear all round).
Check: with the head on a drum, nothing thicker than 8 mm passes under the skirt; the guard is on before the crank is turned.
REV | DESCRIPTION | DATE | BY
P1 | Making sketch for the prototype build plan | 2026-10-03 | AC
DRUMPANEL | github.com/BoujeeEnjinia1701/drumpanel

## DrumPanel disc guard: making sketch

DRAWING NO.
DMP-DWG-111

REV
P1

SHEET
1 of 1

SIZE

## ANSI B

SCALE
1:1

UNITS
mm
PROJECTION | DATE
2026-10-03

DRAWN
Amish Chadha

MATERIAL / NOTES
1.5 mm steel sheet, folded and welded
Licensed CERN-OHL-S-2.0 · Design Molecule Lab · designmolecule.com | Generated from cad/src; do not edit by hand
