BoujeeEnjinia1701/drumpanel/cad/drawings/DMP-DWG-112.pdf

### BUILD PLAN SKETCH, PLAN NOT YET BUILT DrumPanel · github.com/BoujeeEnjinia1701/drumpanel

FRONT VIEW
Scale 1:5; looking at the front (along +Y)

TOP VIEW
Scale 1:5; looking down (along -Z)

RIGHT VIEW
Scale 1:5; looking at the right side (along -X)

256

168 208

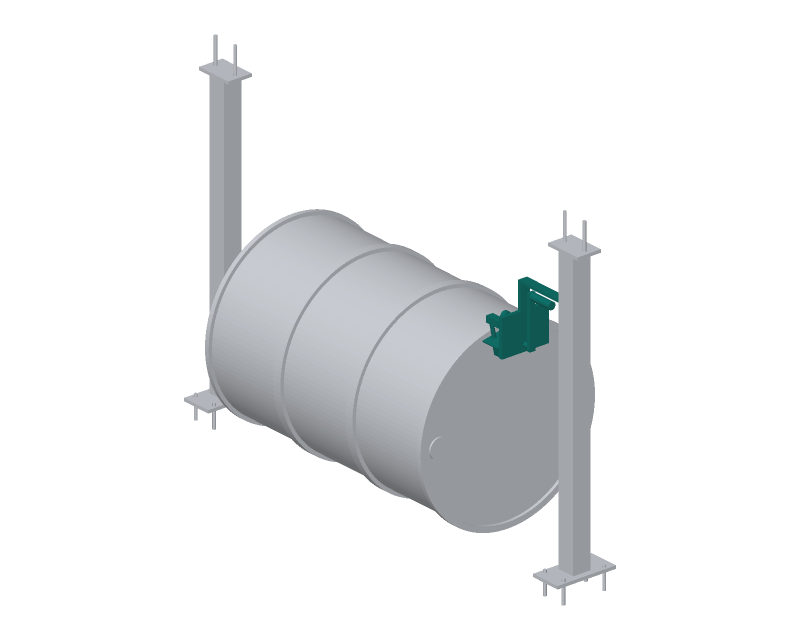
[picture p78: figure]

WHERE IT GOES
This part in colour, its neighbours in grey

HOW TO MAKE IT AND HOW IT FITS
Body: 12 mm plate 160 x 120 mm, standing across the drum end. Drive shaft 16 mm in a 17 mm hole 20 mm up from the body's bottom edge; on it a 40 mm knurled wheel 8 mm wide that bears on the inside of the chime, and a 150 mm crank outside the body.
Guide roller 30 mm on a 12 mm axle, 53.5 mm above the drive shaft, runs on the outside of the chime: chime pinched between the two. Cutter arm: 12 mm rod from a link block on the body, 12 degrees round from the top, carrying the 50 mm hardened wheel square to the head, 4 mm inside the chime wall. An M12 clamp screw presses it into the head; a 1.5 mm cover sits over the wheel.
Torque arm: 30 x 8 mm flat, riser 88 mm, then 170 mm to the post. Check: on a drum the wheel cuts the head just inside the chime; the torque arm rests on the post as the crank turns.
REV | DESCRIPTION | DATE | BY
P1 | Making sketch for the prototype build plan | 2026-10-03 | AC
DRUMPANEL | github.com/BoujeeEnjinia1701/drumpanel

## DrumPanel end cutter: making sketch

DRAWING NO.
DMP-DWG-112

REV
P1

SHEET
1 of 1

SIZE

## ANSI B

SCALE
1:5

UNITS
mm
PROJECTION | DATE
2026-10-03

DRAWN
Amish Chadha

MATERIAL / NOTES
12 mm plate; 16 and 12 mm bar; 30 x 8 mm flat; bought 50 mm cutter wheel
Licensed CERN-OHL-S-2.0 · Design Molecule Lab · designmolecule.com | Generated from cad/src; do not edit by hand
