BoujeeEnjinia1701/drumpanel/cad/drawings/DMP-DWG-113.pdf

### BUILD PLAN SKETCH, PLAN NOT YET BUILT DrumPanel · github.com/BoujeeEnjinia1701/drumpanel

FRONT VIEW
Scale 1:10; looking at the front (along +Y)

TOP VIEW
Scale 1:10; looking down (along -Z)

RIGHT VIEW
Scale 1:10; looking at the right side (along -X)

1120

800 60

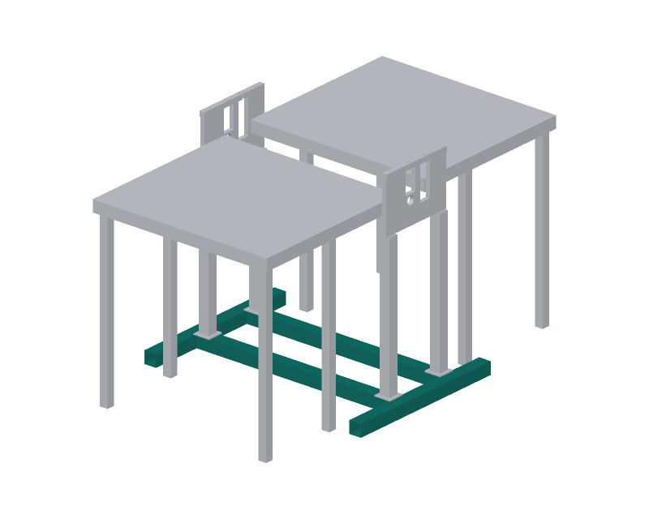
[picture p79: figure]

WHERE IT GOES
This part in colour, its neighbours in grey

HOW TO MAKE IT AND HOW IT FITS
Two cross rails 800 mm long, 1,060 mm apart (centres).
Two long rails 1,000 mm between them, at 120 mm in front of and 190 mm behind the pinch line (centres), flush on top.
Weld on a flat floor or table; diagonals within 2 mm.
Holes: four 13 mm holes in each long rail for the side frame feet (two per foot, 50 mm apart), 467.5 mm each side of the middle. Fit: the side frame legs stand on foot plates bolted to the long rails with 2 x M12 each. The cross rails stick out 400 mm each way so the stand cannot tip.
Check: rocks on no corner on a flat floor; shim if needed.
REV | DESCRIPTION | DATE | BY
P1 | Making sketch for the prototype build plan | 2026-10-03 | AC
DRUMPANEL | github.com/BoujeeEnjinia1701/drumpanel

## DrumPanel roll stand base: making sketch

DRAWING NO.
DMP-DWG-113

REV
P1

SHEET
1 of 1

SIZE

## ANSI B

SCALE
1:10

UNITS
mm
PROJECTION | DATE
2026-10-03

DRAWN
Amish Chadha

MATERIAL / NOTES
60 x 60 x 3 mm RHS, S275
Licensed CERN-OHL-S-2.0 · Design Molecule Lab · designmolecule.com | Generated from cad/src; do not edit by hand
