BoujeeEnjinia1701/drumpanel/cad/drawings/DMP-DWG-114.pdf

### BUILD PLAN SKETCH, PLAN NOT YET BUILT DrumPanel · github.com/BoujeeEnjinia1701/drumpanel

FRONT VIEW
Scale 1:10; looking at the front (along +Y)

TOP VIEW
Scale 1:10; looking down (along -Z)

RIGHT VIEW
Scale 1:10; looking at the right side (along -X)

80

390 950

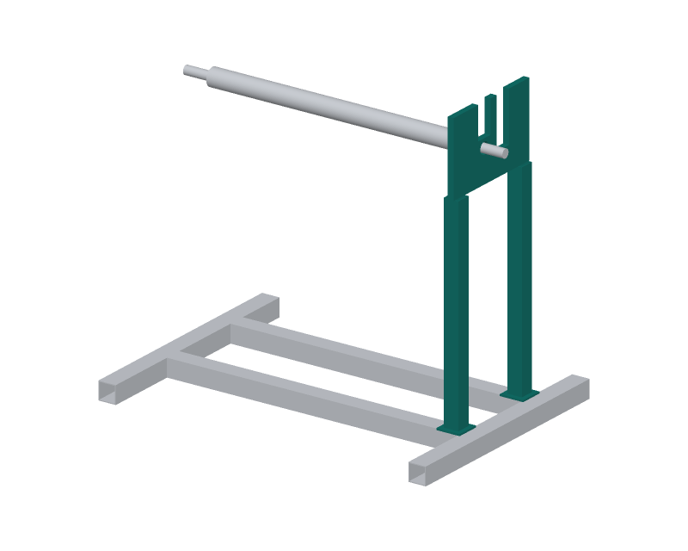
[picture p80: figure]

WHERE IT GOES
This part in colour, its neighbours in grey

HOW TO MAKE IT AND HOW IT FITS
Make two (mirror pair). Plate 20 mm, 370 x 250 mm.
Bore 40 mm for the lower roll bush: 110 mm up from the plate's bottom edge, 150 mm from its front edge.
Pinch slot 60 mm wide from 140 mm up to the top, centred over the bore. Bending slot 60 mm wide from 80 mm up to the top, centred 90 mm behind the bore. File both slots smooth and parallel.
Legs: 50 x 50 x 3 RHS 694 mm long under the plate at 30 mm and 340 mm from the front edge, with 80 x 80 x 6 mm foot plates.
Top bridge (bolted, not welded): 25 x 25 mm bar 370 mm long with M16 and M20 threaded holes over the slots; 2 x M10 into the plate. Fit: plate inner faces 920 mm apart; legs bolted to the base. Check: both bores line up within 0.5 mm (a 30 mm bar through).
REV | DESCRIPTION | DATE | BY
P1 | Making sketch for the prototype build plan | 2026-10-03 | AC
DRUMPANEL | github.com/BoujeeEnjinia1701/drumpanel

## DrumPanel side frame (make 2, mirror pair): making sketch

DRAWING NO.
DMP-DWG-114

REV
P1

SHEET
1 of 1

SIZE

## ANSI B

SCALE
1:10

UNITS
mm
PROJECTION | DATE
2026-10-03

DRAWN
Amish Chadha

MATERIAL / NOTES
20 mm plate 370 x 250; 50 x 50 x 3 RHS legs; 6 mm foot plates; S275
Licensed CERN-OHL-S-2.0 · Design Molecule Lab · designmolecule.com | Generated from cad/src; do not edit by hand
