BoujeeEnjinia1701/drumpanel/cad/drawings/DMP-DWG-115.pdf

### BUILD PLAN SKETCH, PLAN NOT YET BUILT DrumPanel · github.com/BoujeeEnjinia1701/drumpanel

FRONT VIEW
Scale 1:10; looking at the front (along +Y)

TOP VIEW
Scale 1:10; looking down (along -Z)

RIGHT VIEW
Scale 1:10; looking at the right side (along -X)

1092

60 60

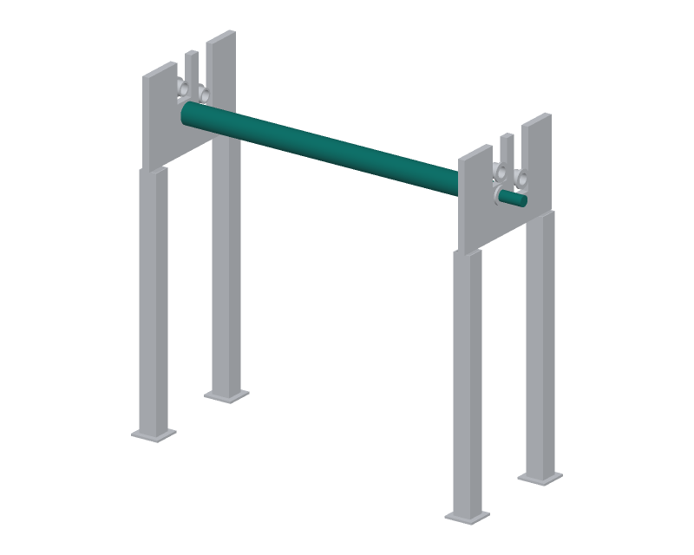
[picture p81: figure]

WHERE IT GOES
This part in colour, its neighbours in grey

HOW TO MAKE IT AND HOW IT FITS
All three rolls: 60 mm bright bar, 900 mm face, ends faced square. Journals turned to 30 mm, a sliding fit in the bronze bushes
(0.05 to 0.10 mm clear). Small fillet at each shoulder.
Lower pinch roll (drawn): 1,092 mm overall; gear-end journal 90 mm, sprocket-end journal 102 mm; keyways for the gear and sprocket. Upper pinch roll: 1,032 mm; gear-end journal 90 mm, other 42 mm; keyway for the gear.
Bending roll: 984 mm; both journals 42 mm; no keyways.
Turn between centres; run-out of the face within 0.05 mm.
Fit: pinch rolls one above the other at 61 mm centres (1 mm sheet); bending roll 90 mm behind, set by its screws. Check: each roll turns freely in its bushes by hand.
REV | DESCRIPTION | DATE | BY
P1 | Making sketch for the prototype build plan | 2026-10-03 | AC
DRUMPANEL | github.com/BoujeeEnjinia1701/drumpanel

## DrumPanel rolls (make 3; the lower pinch roll drawn): making sketch

DRAWING NO.
DMP-DWG-115

REV
P1

SHEET
1 of 1

SIZE

## ANSI B

SCALE
1:10

UNITS
mm
PROJECTION | DATE
2026-10-03

DRAWN
Amish Chadha

MATERIAL / NOTES
60 mm bright bar C45 (EN8)
Licensed CERN-OHL-S-2.0 · Design Molecule Lab · designmolecule.com | Generated from cad/src; do not edit by hand
