BoujeeEnjinia1701/drumpanel/cad/drawings/DMP-DWG-117.pdf

### BUILD PLAN SKETCH, PLAN NOT YET BUILT DrumPanel · github.com/BoujeeEnjinia1701/drumpanel

FRONT VIEW
Scale 1:5; looking at the front (along +Y)

TOP VIEW
Scale 1:5; looking down (along -Z)

RIGHT VIEW
Scale 1:5; looking at the right side (along -X)

185

190 374

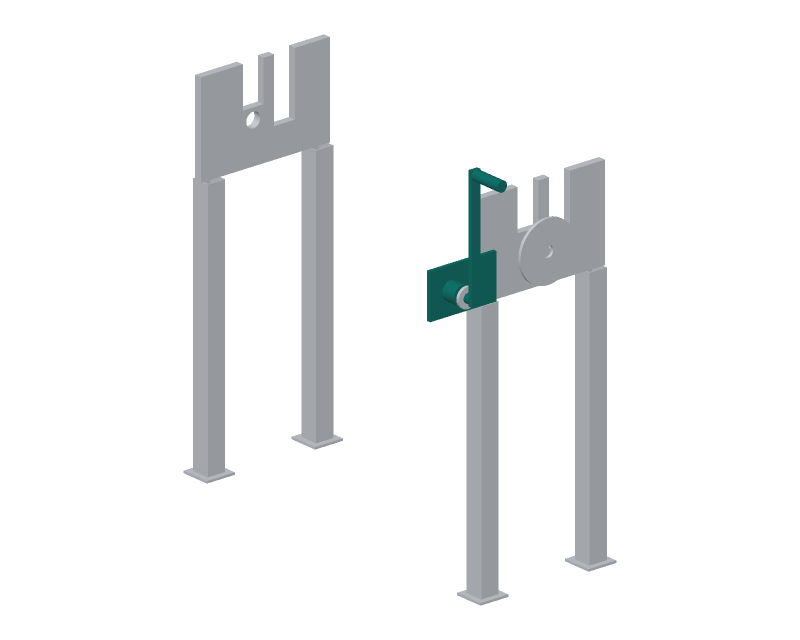
[picture p82: figure]

WHERE IT GOES
This part in colour, its neighbours in grey

HOW TO MAKE IT AND HOW IT FITS
Bracket: 10 mm plate 190 x 120 mm, bolted to the outer face of the right-hand side frame (front prong) with 4 x M10.
Housing: 50 mm round bar 40 mm long bored 26 mm for two bronze bushes, welded square to the bracket, 230 mm in front of the
pinch line and 50 mm below the lower roll centre.
Crank shaft: 25 mm, 90 mm long; keyway for the 13 tooth sprocket. Crank: arm 24 x 12 mm, 300 mm between centres; 28 mm grip 88 mm long, free to spin.
Sprockets #40: 13 teeth on the crank shaft, 39 teeth on the lower roll; line them up with a straightedge; chain slack 5 mm.
Fit: the chain guard bolts over both sprockets.
Check: one crank turn moves the sheet 63 mm.
REV | DESCRIPTION | DATE | BY
P1 | Making sketch for the prototype build plan | 2026-10-03 | AC
DRUMPANEL | github.com/BoujeeEnjinia1701/drumpanel

## DrumPanel crank bracket and crank: making sketch

DRAWING NO.
DMP-DWG-117

REV
P1

SHEET
1 of 1

SIZE

## ANSI B

SCALE
1:5

UNITS
mm
PROJECTION | DATE
2026-10-03

DRAWN
Amish Chadha

MATERIAL / NOTES
10 mm plate; 50 mm bar; 25 mm shaft; 24 x 12 mm flat
Licensed CERN-OHL-S-2.0 · Design Molecule Lab · designmolecule.com | Generated from cad/src; do not edit by hand
