BoujeeEnjinia1701/drumpanel/cad/drawings/DMP-DWG-118.pdf

### BUILD PLAN SKETCH, PLAN NOT YET BUILT DrumPanel · github.com/BoujeeEnjinia1701/drumpanel

FRONT VIEW
Scale 1:10; looking at the front (along +Y)

TOP VIEW
Scale 1:10; looking down (along -Z)

RIGHT VIEW
Scale 1:10; looking at the right side (along -X)

1105

417 222

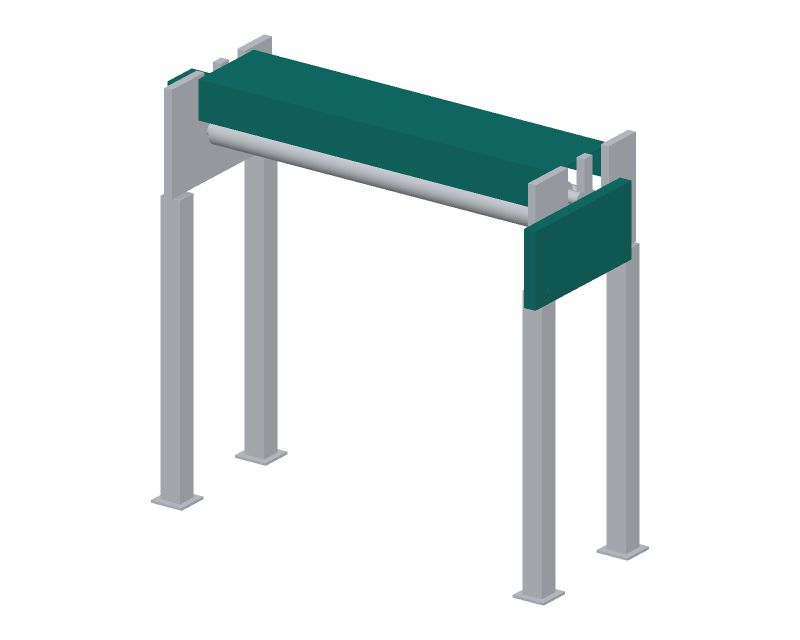
[picture p83: figure]

WHERE IT GOES
This part in colour, its neighbours in grey

HOW TO MAKE IT AND HOW IT FITS
In-feed guard: 920 x 92 mm, 50 mm in front of the pinch line; its lower edge 8 mm above the in-feed table, rolled to a 4 mm radius. Out-feed guard: 920 x 79 mm, 150 mm behind the pinch line, lower edge 8 mm above the out-feed table.
Lid: 920 x 204 mm, joining the two guards over the rolls.
Chain guard: a box 30 x 355 x 180 mm round both sprockets, with holes for the shafts; bolted to the crank bracket housing.
Gear guard: a box 65 x 90 x 145 mm over the pinch gears, bolted to the left-hand side frame.
All guards held by M6 screws: a tool is needed to take them off. Check: a 10 mm rod cannot reach any nip, gear or sprocket.
REV | DESCRIPTION | DATE | BY
P1 | Making sketch for the prototype build plan | 2026-10-03 | AC
DRUMPANEL | github.com/BoujeeEnjinia1701/drumpanel

## DrumPanel roll guards: making sketch

DRAWING NO.
DMP-DWG-118

REV
P1

SHEET
1 of 1

SIZE

## ANSI B

SCALE
1:10

UNITS
mm
PROJECTION | DATE
2026-10-03

DRAWN
Amish Chadha

MATERIAL / NOTES
1.5 mm steel sheet, folded; M6 screws
Licensed CERN-OHL-S-2.0 · Design Molecule Lab · designmolecule.com | Generated from cad/src; do not edit by hand
