BoujeeEnjinia1701/drumpanel/cad/drawings/DMP-DWG-119.pdf

### BUILD PLAN SKETCH, PLAN NOT YET BUILT DrumPanel · github.com/BoujeeEnjinia1701/drumpanel

FRONT VIEW
Scale 1:25; looking at the front (along +Y)

TOP VIEW
Scale 1:25; looking down (along -Z)

RIGHT VIEW
Scale 1:25; looking at the right side (along -X)

900

1785 913

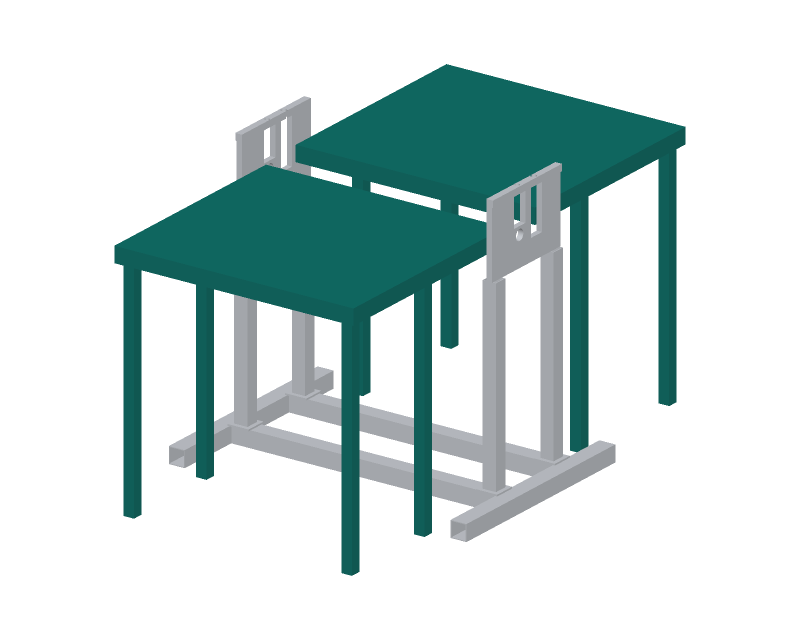
[picture p84: figure]

WHERE IT GOES
This part in colour, its neighbours in grey

HOW TO MAKE IT AND HOW IT FITS
In-feed table: plywood 900 x 815 mm on an angle frame, four RHS legs; top 900 mm from the floor, level with the top of the
lower roll; front edge 35 mm short of the roll.
Out-feed table: plywood 900 x 810 mm on a similar frame; top 913 mm from the floor, level with the top of the bending roll at its usual setting; starts 125 mm behind the pinch line.
Legs: 40 x 40 x 3 RHS with M10 levelling screws.
Seal the plywood; countersink the screws so the panels do not catch.
Check: a straightedge from each table to its roll shows no step over 1 mm.
REV | DESCRIPTION | DATE | BY
P1 | Making sketch for the prototype build plan | 2026-10-03 | AC
DRUMPANEL | github.com/BoujeeEnjinia1701/drumpanel

## DrumPanel in-feed and out-feed tables: making sketch

DRAWING NO.
DMP-DWG-119

REV
P1

SHEET
1 of 1

SIZE

## ANSI B

SCALE
1:25

UNITS
mm
PROJECTION | DATE
2026-10-03

DRAWN
Amish Chadha

MATERIAL / NOTES
18 mm exterior plywood; 40 x 40 x 3 mm angle and RHS
Licensed CERN-OHL-S-2.0 · Design Molecule Lab · designmolecule.com | Generated from cad/src; do not edit by hand
