BoujeeEnjinia1701/drumpanel/cad/drawings/DMP-DWG-001.png

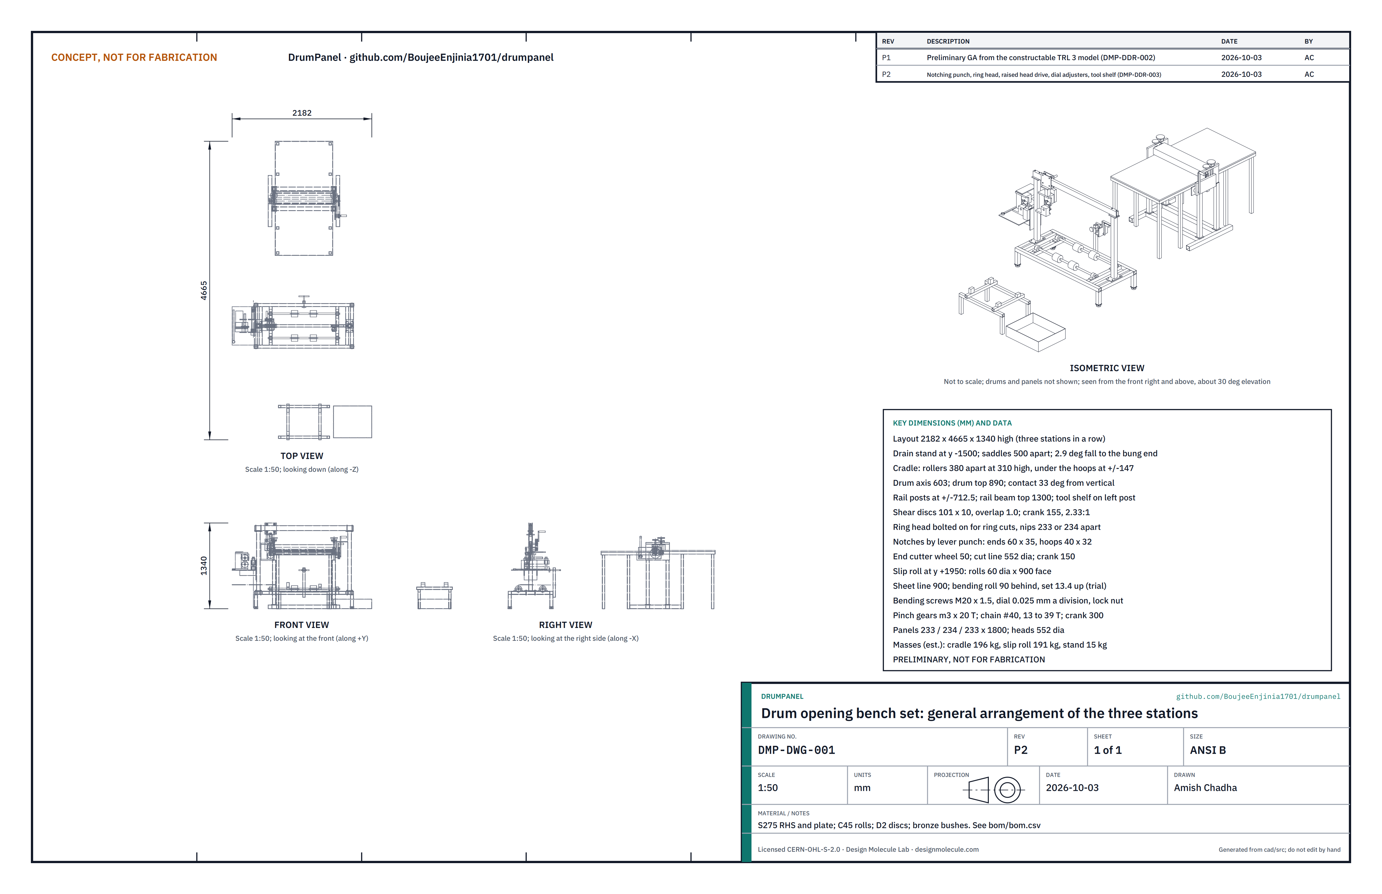
cad/drawings/DMP-DWG-001.png
