BoujeeEnjinia1701/drumpanel/media/card.png

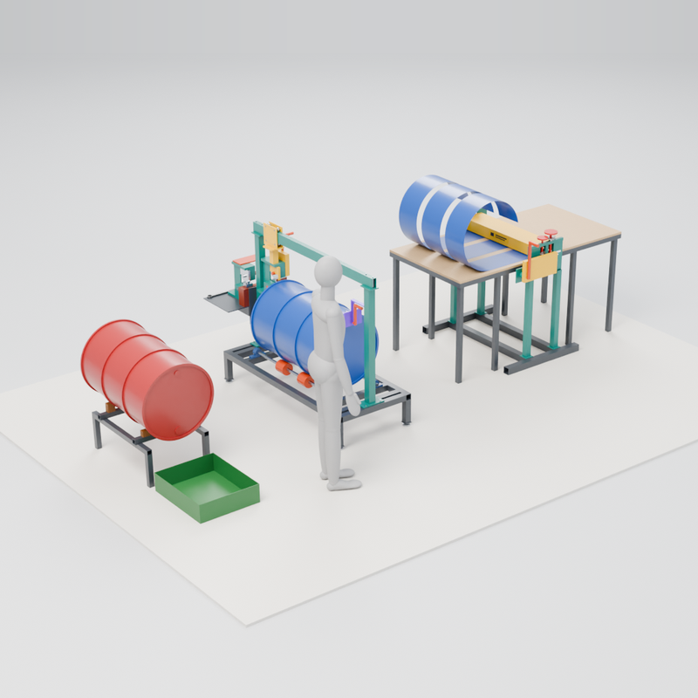
media/card.png
