BoujeeEnjinia1701/drumpanel/media/concept-blueprint.png

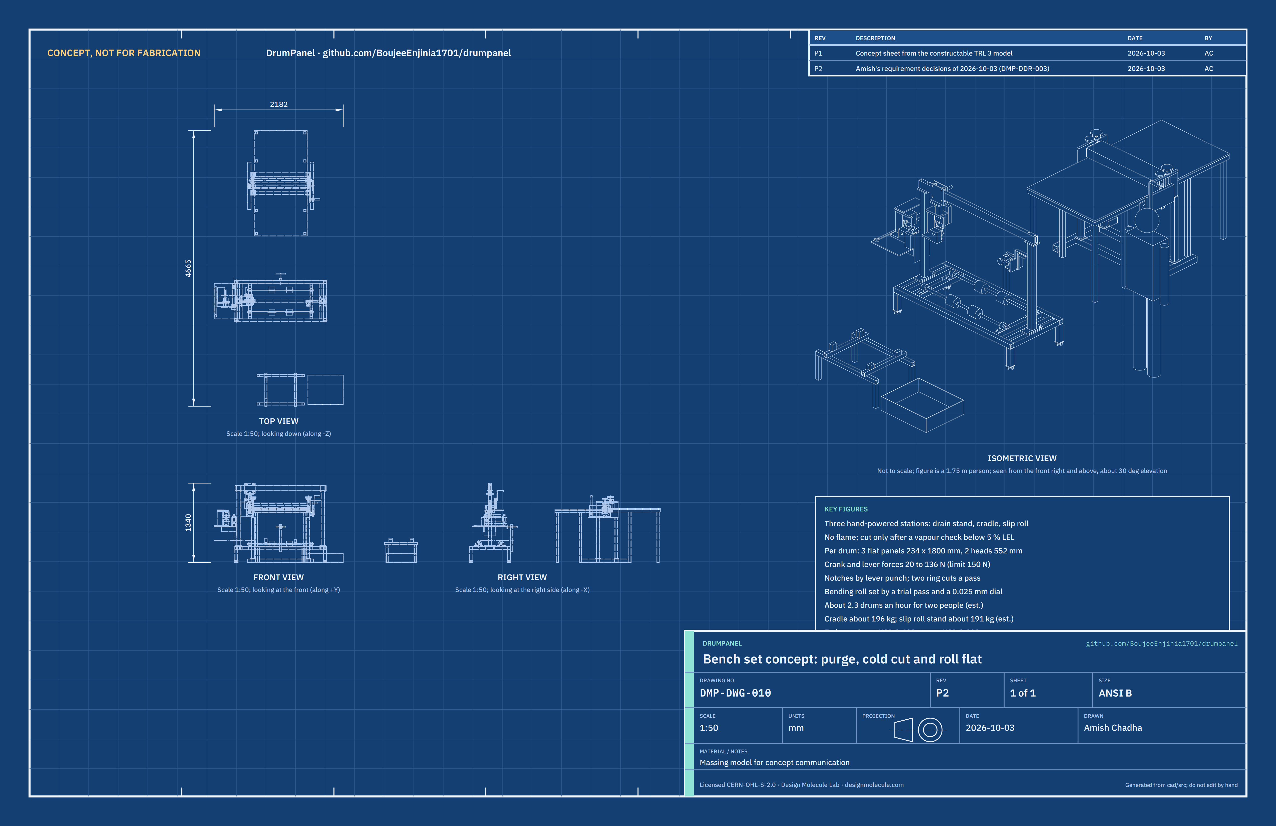
media/concept-blueprint.png
