BoujeeEnjinia1701/drumpanel/media/cutaway.png

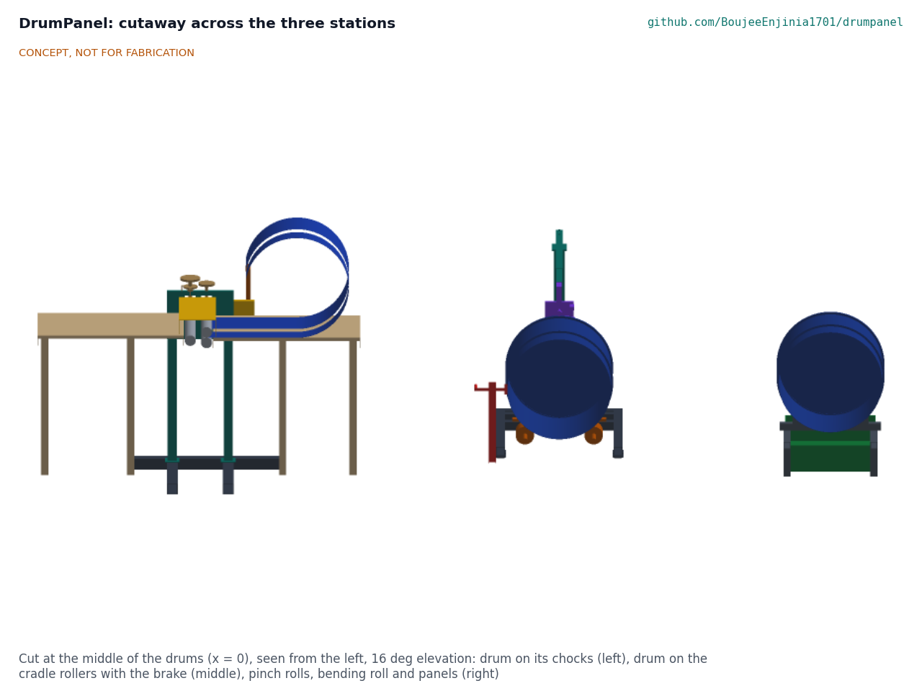
media/cutaway.png
