BoujeeEnjinia1701/drumpanel/media/exploded.png

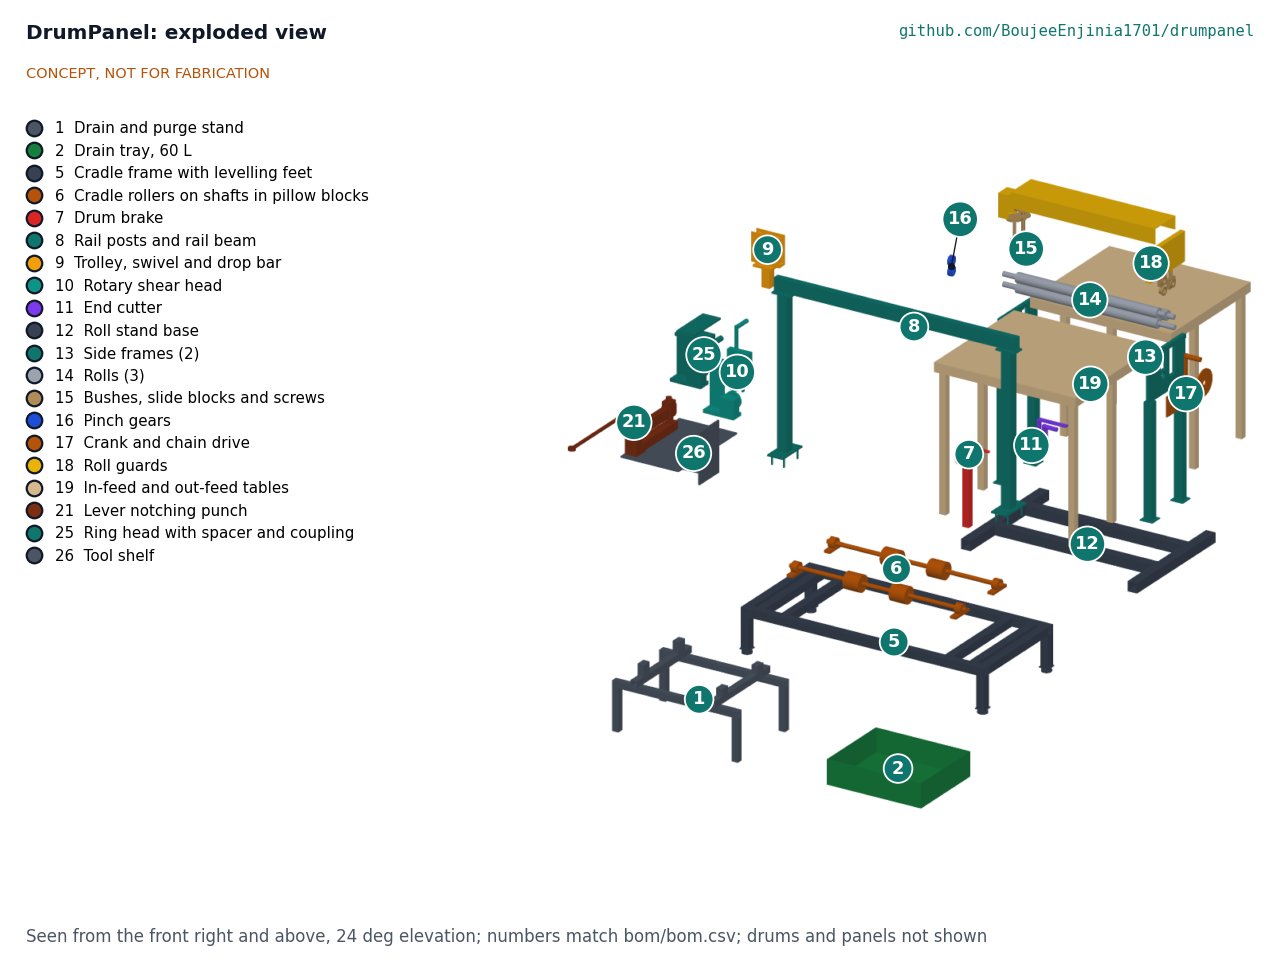
media/exploded.png
