BoujeeEnjinia1701/drumpanel/media/flow.png

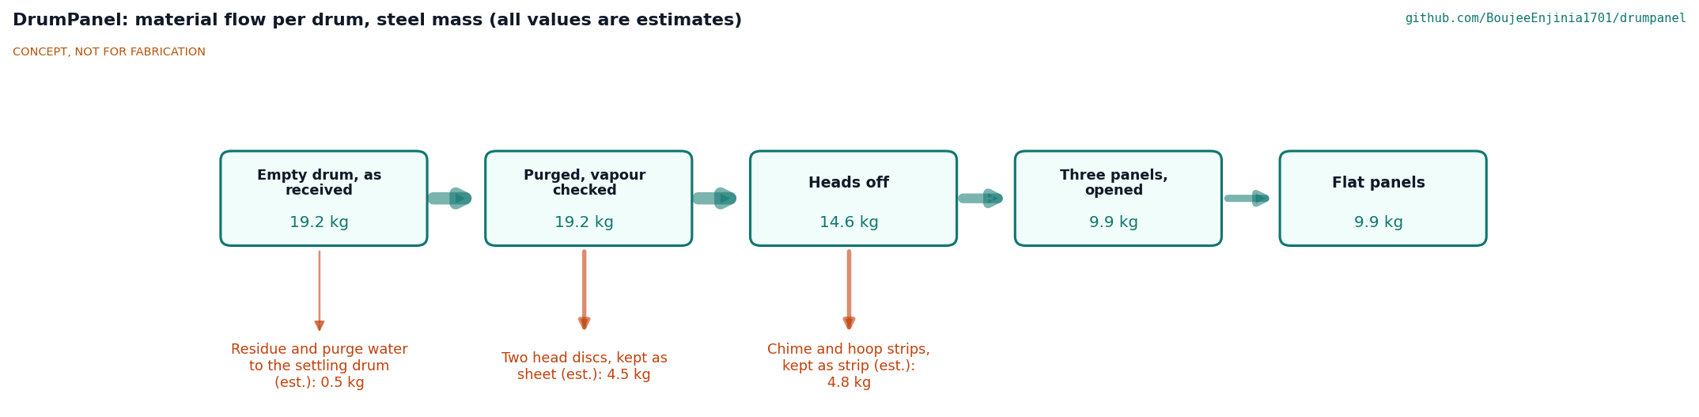
media/flow.png
