BoujeeEnjinia1701/drumpanel/media/render-detail.png

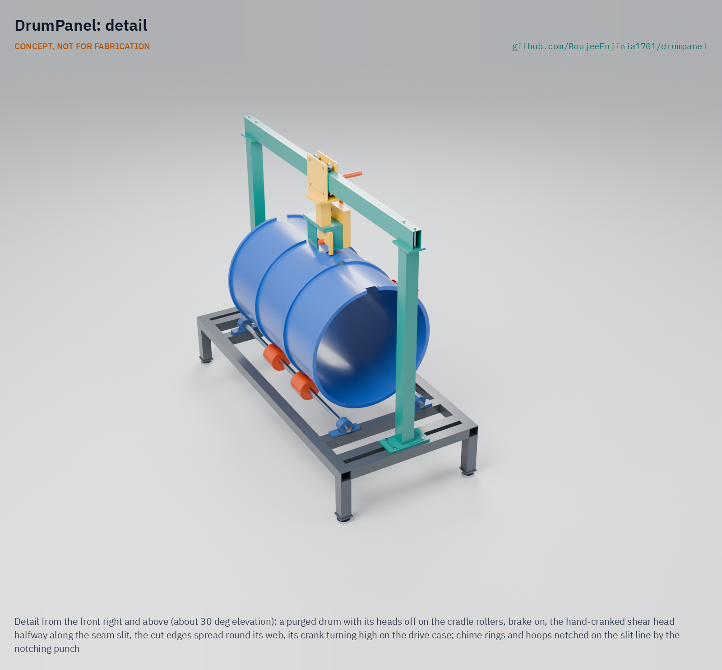
media/render-detail.png
