BoujeeEnjinia1701/drumpanel/media/render-exploded.png

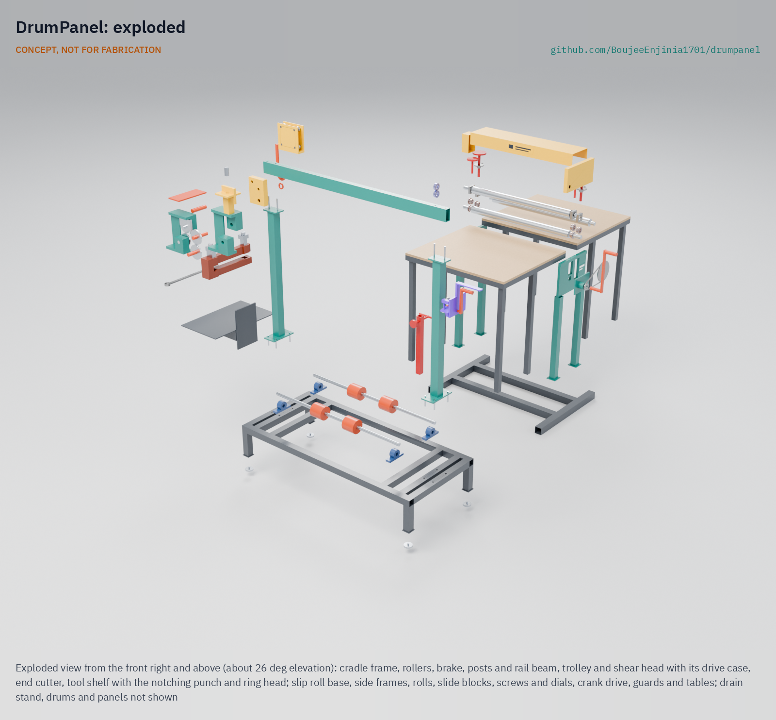
media/render-exploded.png
