BoujeeEnjinia1701/drumpanel/media/social-preview.png

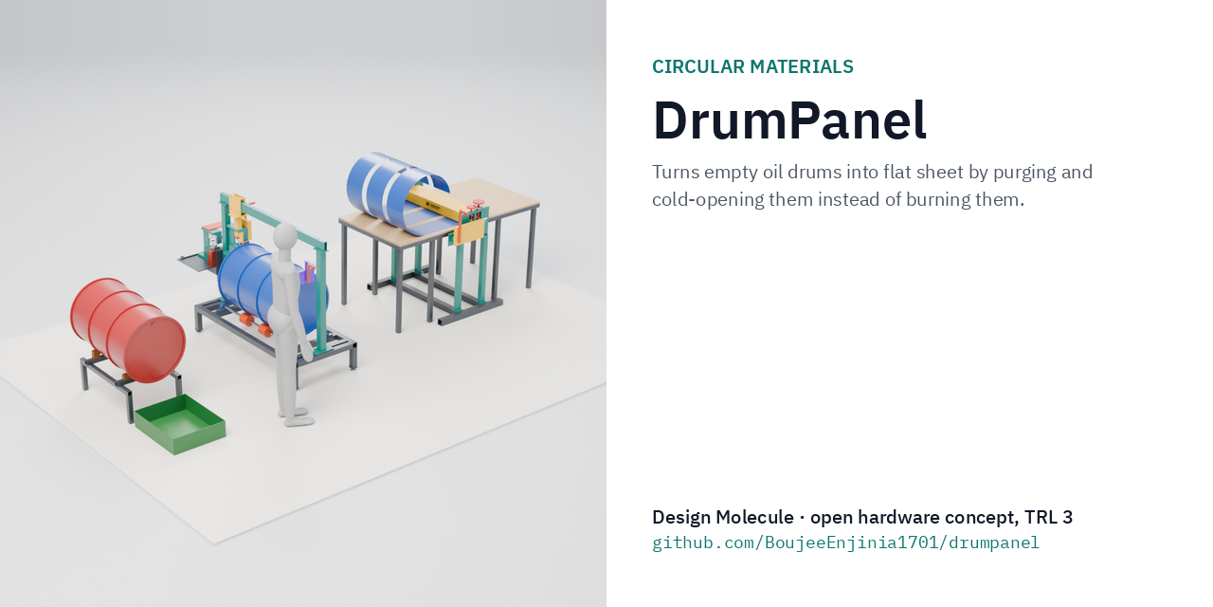
media/social-preview.png
